felipesantiagoach-ops/cdp1802-8bit-computer/informe/Codigo fuente/contenido/reconocimientos.tex

% LOS RECONOCIMIENTOS
% -------------------

% Aquí se escribe la dedicatoria del proyecto y los agradecimientos. El entorno 'reconocimiento' tiene la estructura \begin{reconocimiento}{Dedicatoria} Agradecimientos \end{reconocimiento}

\begin{reconocimiento}{Dedicado a nuestras familias y amigos.}

\lipsum[5]

\begin{flushright}
\textit{Alegre Chamorro, Felipe Santiago}
\end{flushright}

\vspace{1cm}

Gracias a mis padres por haber hecho posible estudiar ingeniería, no habría sido posible sin ellos, y gracias a los amigos que hice y a las experiencias que tuvimos durante el transcurso de la carrera, que son, para mí, casi más importantes que la carrera en sí misma.

\begin{flushright}
\textit{Boher, Atilio}
\end{flushright}

\vspace{1cm}

\lipsum[5]

\begin{flushright}
\textit{Vera, Uriel Adrián}
\end{flushright}

\end{reconocimiento}
