felipesantiagoach-ops/cdp1802-8bit-computer/programas/sistema medio/Tx/notas.txt

no funcionaron en el sistema medio, si funicionaron algunos en el simulador, pero no se testearon todos
