felipesantiagoach-ops/cdp1802-8bit-computer/Poster_PyD_2022_Grupo_A.pdf

## ¿ COMO ERAN LAS PRIMERAS COMPUTADORAS ? COMPUTADORA BASADA EN EL PRIMER

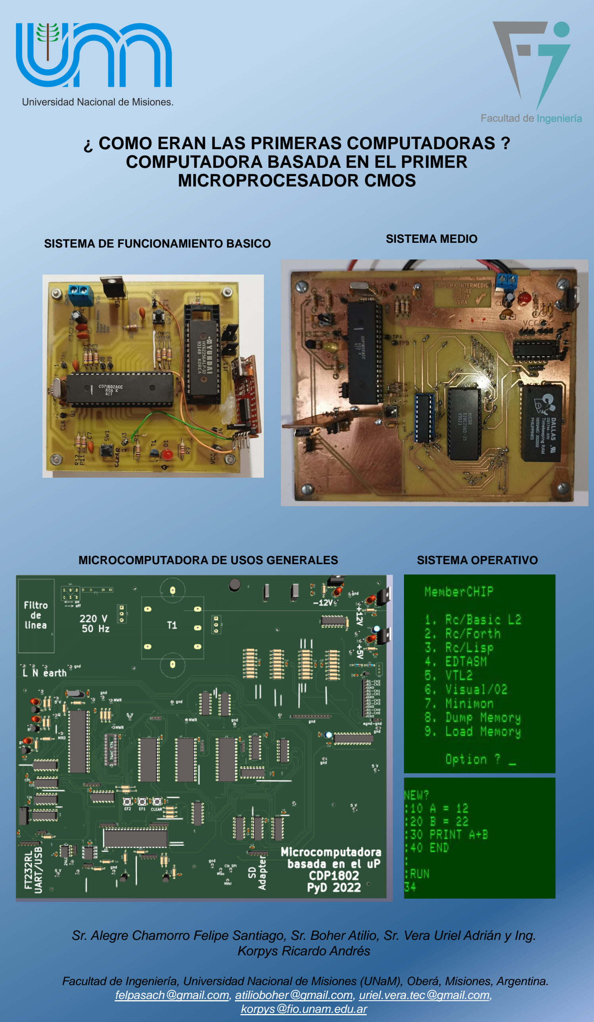
[picture p131: page 1]

## MICROPROCESADOR CMOS

SISTEMA DE FUNCIONAMIENTO BASICO

Sr. Alegre Chamorro Felipe Santiago, Sr. Boher Atilio, Sr. Vera Uriel Adrián y Ing. Korpys Ricardo Andrés

Facultad de Ingeniería, Universidad Nacional de Misiones (UNaM), Oberá, Misiones, Argentina. felpasach@gmail.com, atilioboher@gmail.com, uriel.vera.tec@gmail.com, korpys@fio.unam.edu.ar

SISTEMA MEDIO

MICROCOMPUTADORA DE USOS GENERALES | SISTEMA OPERATIVO
