felipesantiagoach-ops/cdp1802-8bit-computer/archivos_de_kicad/3_Sistema_final/PCB1.pdf

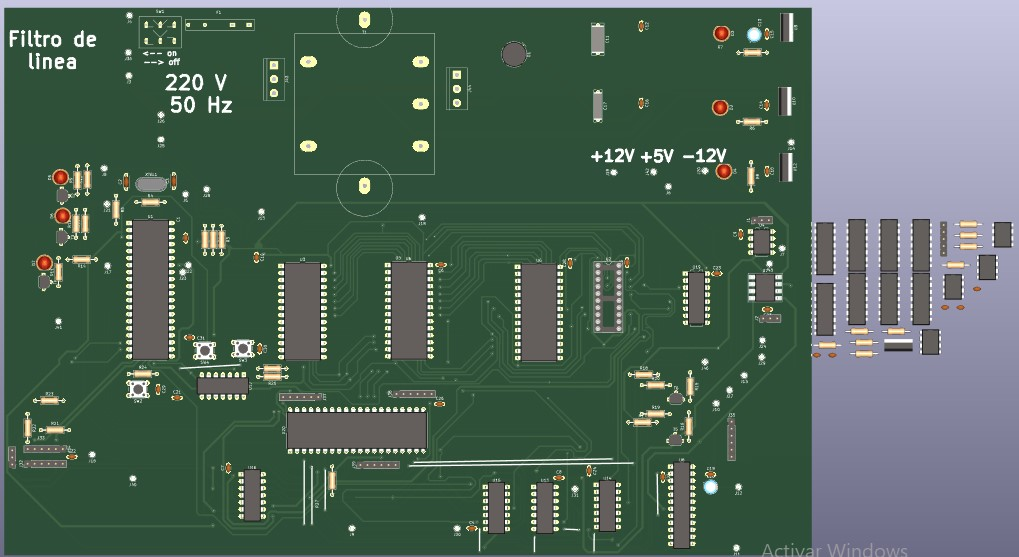
[picture p132: figure]
