felipesantiagoach-ops/cdp1802-8bit-computer/programas/sistema minimo/comunicacion serial/funcionamiento Tx serial.png

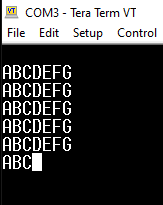
programas/sistema minimo/comunicacion serial/funcionamiento Tx serial.png
