felipesantiagoach-ops/cdp1802-8bit-computer/informe/Codigo fuente/imagenes/programa_1.pdf

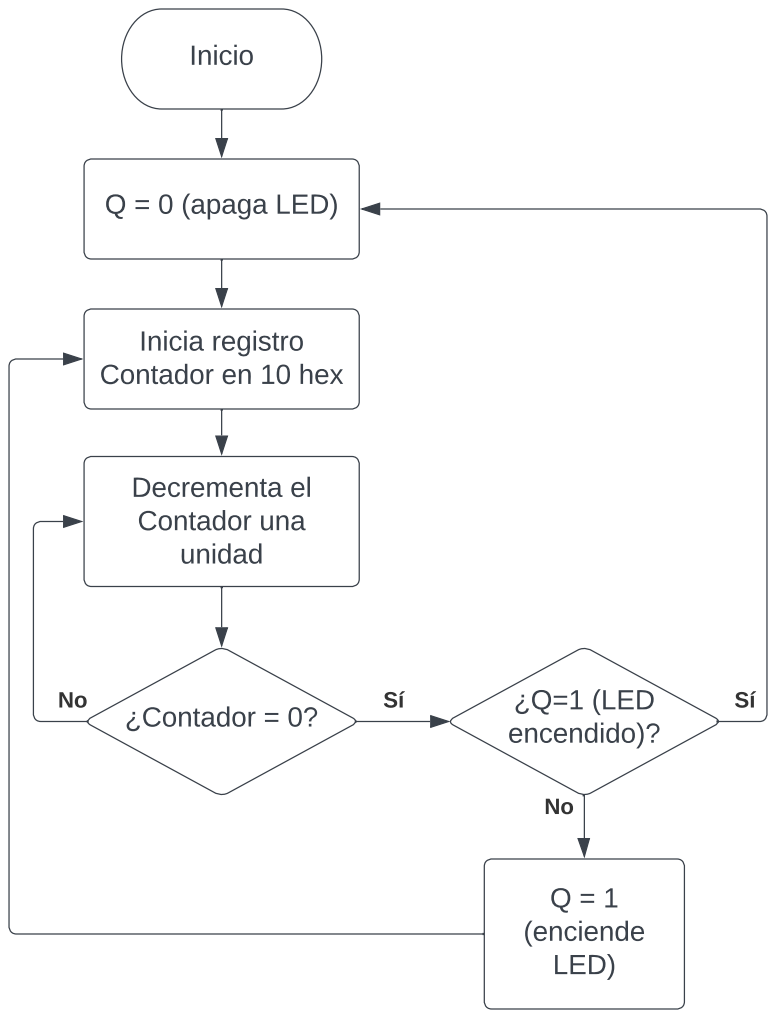
[picture p139: page 1]
Inicio; Q = 0 (apaga LED); Decrementa el Contador una unidad; ¿Contador = 0?; ¿Q=1 (LED; encendido)?; Q = 1 (enciende LED)

Inicia registro
Contador en 10 hex
