felipesantiagoach-ops/cdp1802-8bit-computer/informe/Codigo fuente/imagenes/programa_2.pdf

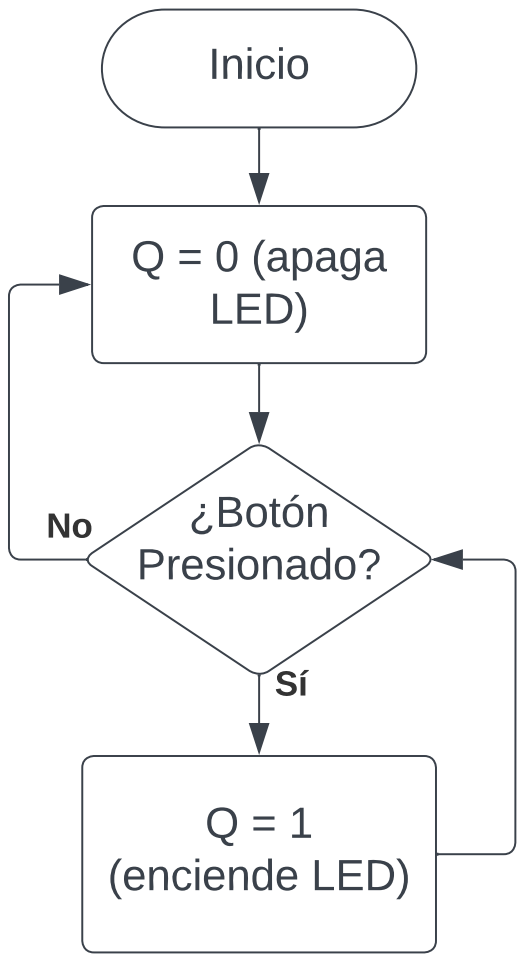
[picture p140: page 1]
Inicio; Q = 0 (apaga LED); ¿Botón Presionado?; Q = 1 (enciende LED)
