felipesantiagoach-ops/cdp1802-8bit-computer/informe/Codigo fuente/imagenes/programa_3.pdf

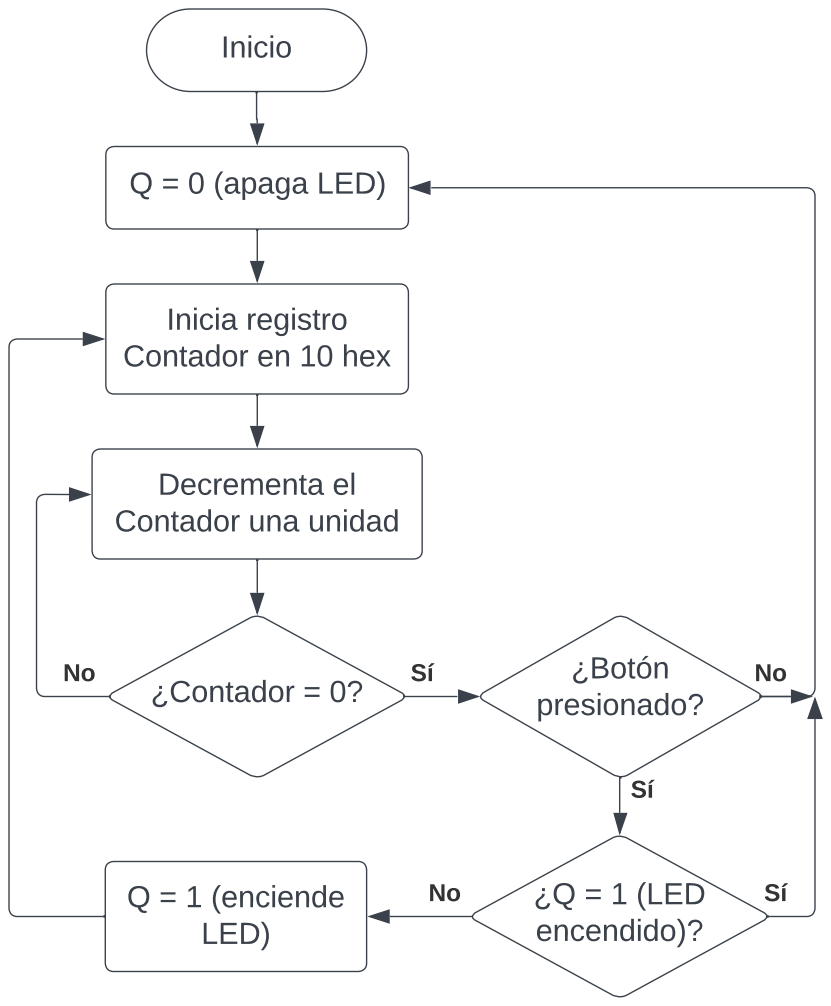
[picture p141: page 1]
Inicio; ¿Contador = 0?; Q = 0 (apaga LED); ¿Q = 1 (LED encendido)?; Q = 1 (enciende LED); ¿Botón presionado?

Inicia registro
Contador en 10 hex

Decrementa el
Contador una unidad
