felipesantiagoach-ops/cdp1802-8bit-computer/informe/Codigo fuente/imagenes/program_4_rut_de_trans.pdf

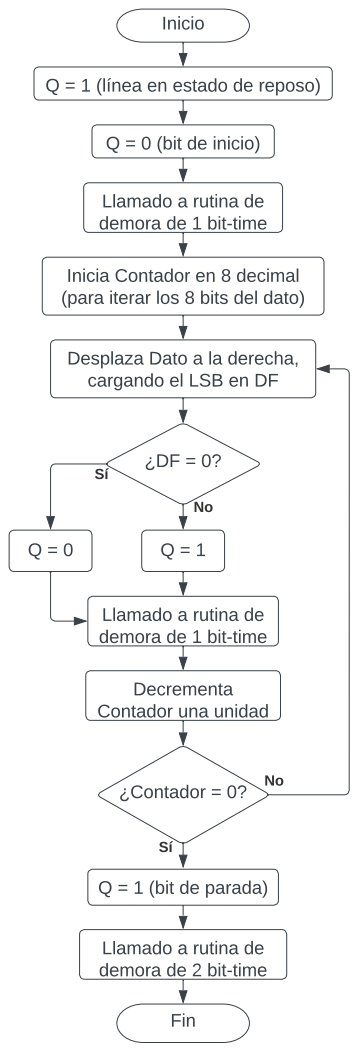
[picture p145: page 1]
Inicio; ¿Contador = 0?; Fin

Q = 1 (línea en estado de reposo)

Q = 0 (bit de inicio)

Llamado a rutina de
demora de 1 bit-time

Inicia Contador en 8 decimal
(para iterar los 8 bits del dato)

Desplaza Dato a la derecha,
cargando el LSB en DF

Decrementa
Contador una unidad

Q = 1 (bit de parada)

demora de 2 bit-time
