felipesantiagoach-ops/cdp1802-8bit-computer/informe/Codigo fuente/imagenes/programa_4_main.pdf

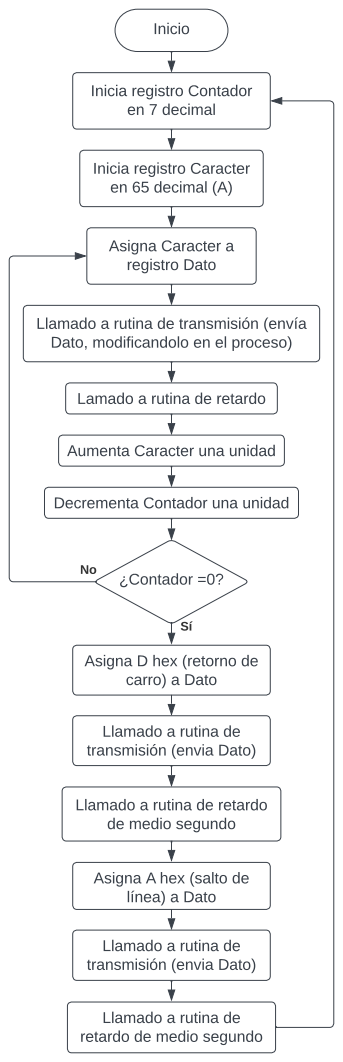
[picture p146: page 1]
Inicio; Asigna Caracter a registro Dato; ¿Contador =0?

Inicia registro Contador
en 7 decimal

Inicia registro Caracter
en 65 decimal (A)

Llamado a rutina de transmisión (envía
Dato, modificandolo en el proceso)

Lamado a rutina de retardo

Aumenta Caracter una unidad

Decrementa Contador una unidad

Asigna D hex (retorno de
carro) a Dato

Llamado a rutina de
transmisión (envia Dato)

Llamado a rutina de retardo
de medio segundo

Asigna A hex (salto de
línea) a Dato

retardo de medio segundo
