felipesantiagoach-ops/cdp1802-8bit-computer/informe/Codigo fuente/imagenes/EsquematicosSF/Esquematico (1).pdf

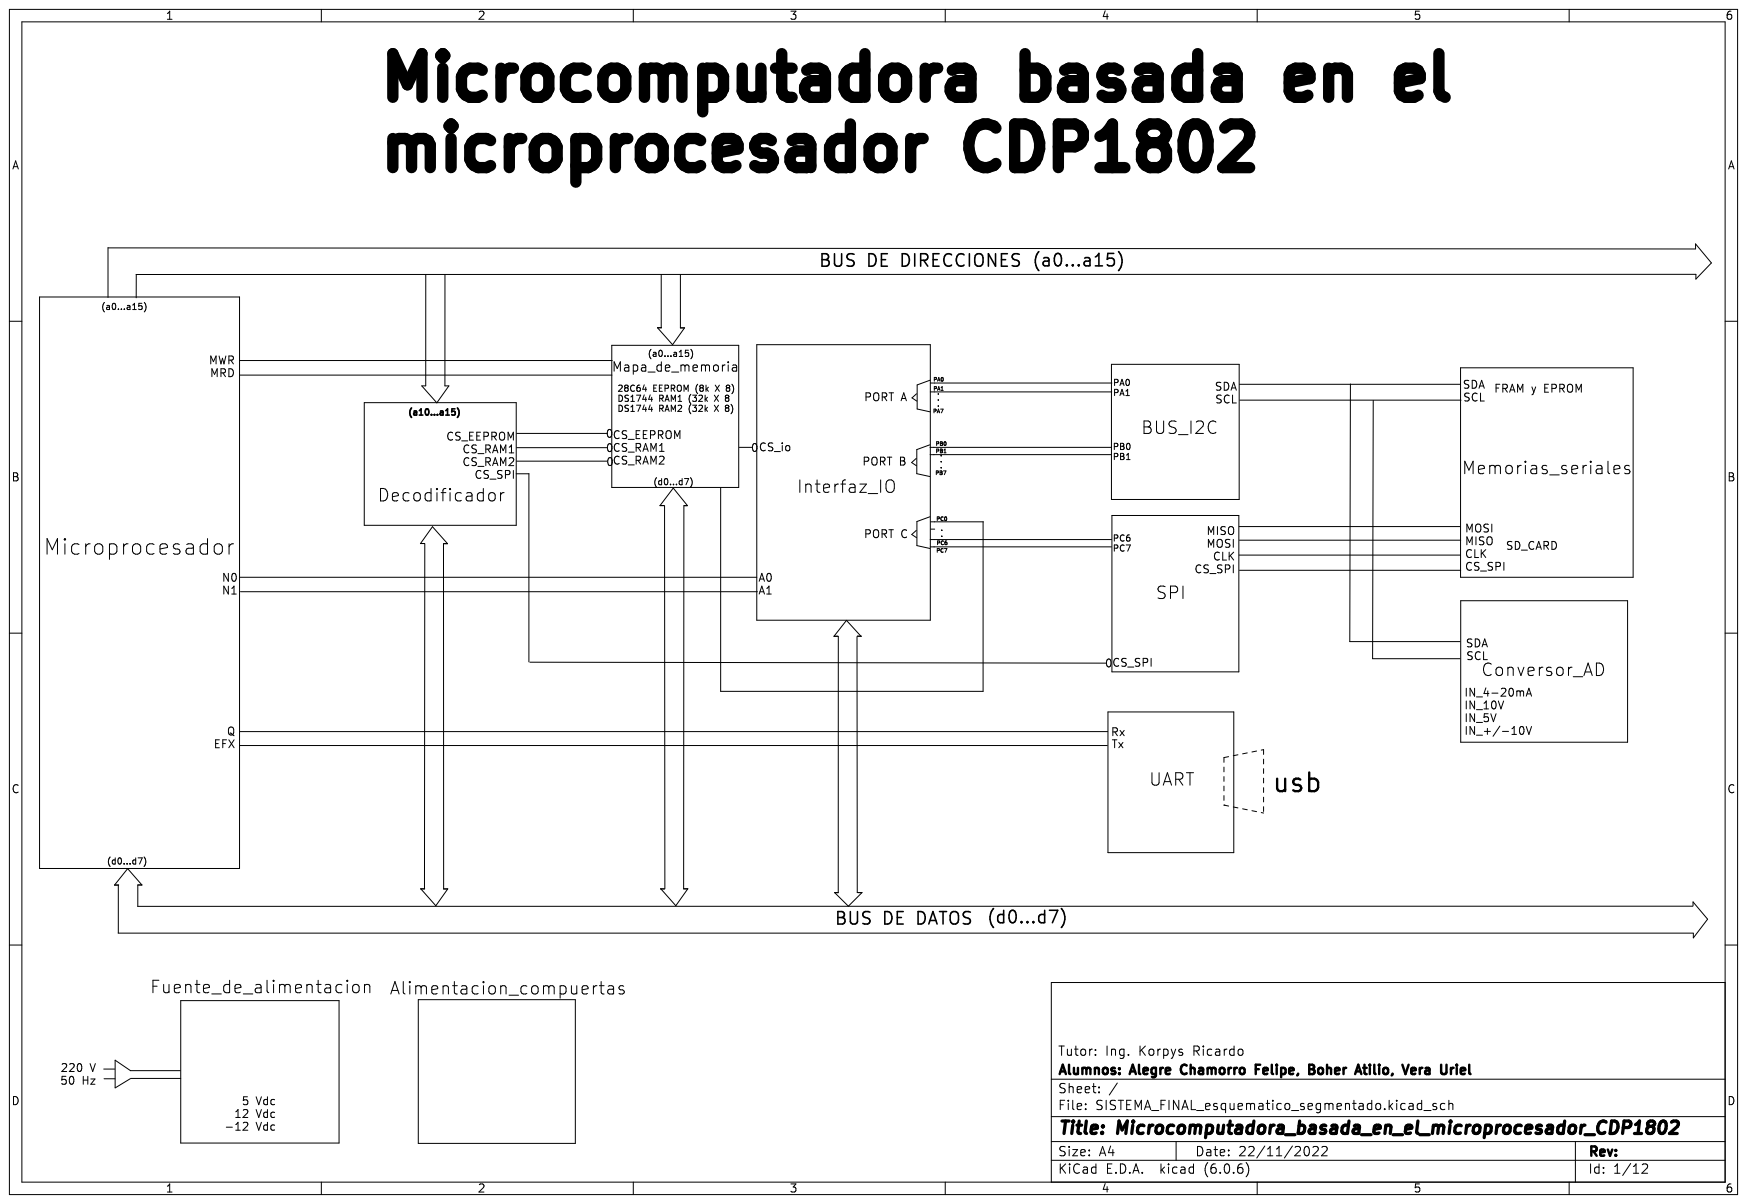
[picture p147: page 1]
