felipesantiagoach-ops/cdp1802-8bit-computer/informe/Codigo fuente/imagenes/EsquematicosSF/Esquematico (10).pdf

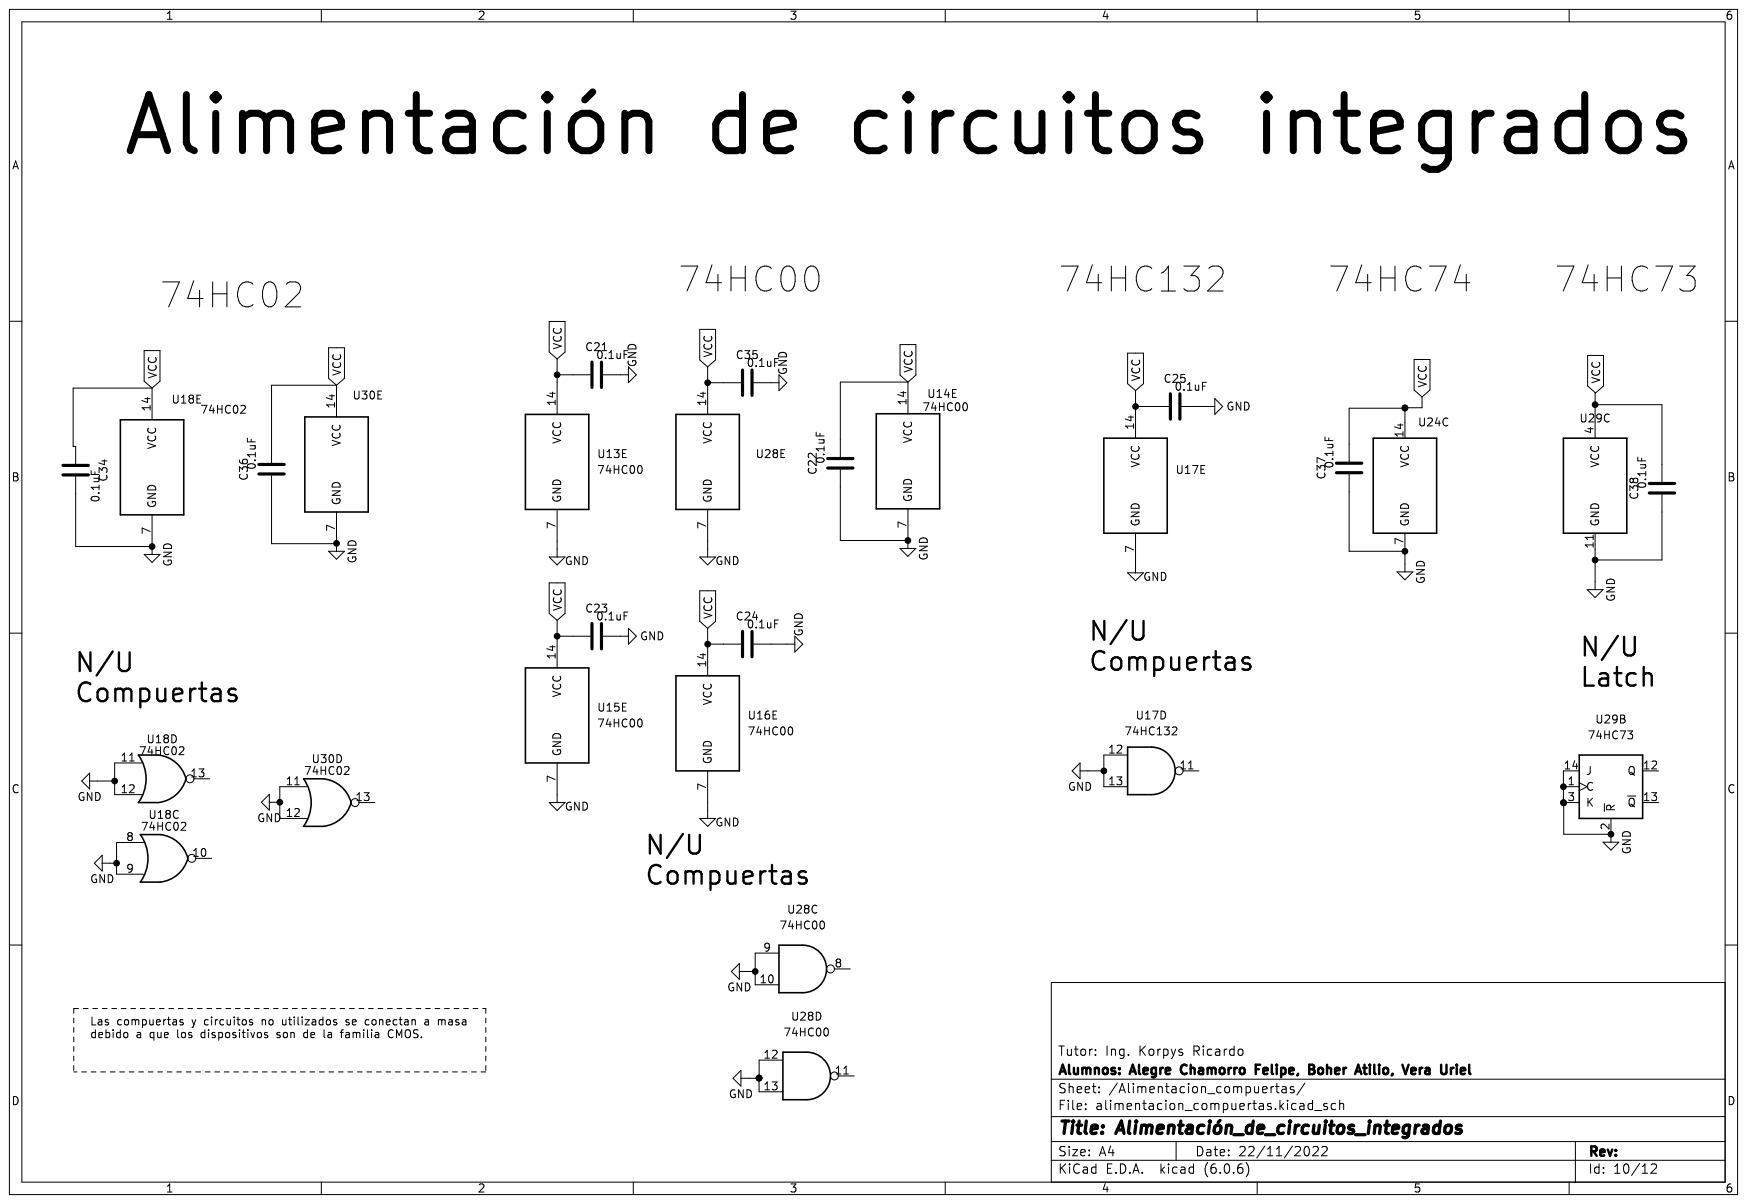
[picture p148: page 1]
