felipesantiagoach-ops/cdp1802-8bit-computer/informe/Codigo fuente/imagenes/EsquematicosSF/Esquematico (11).pdf

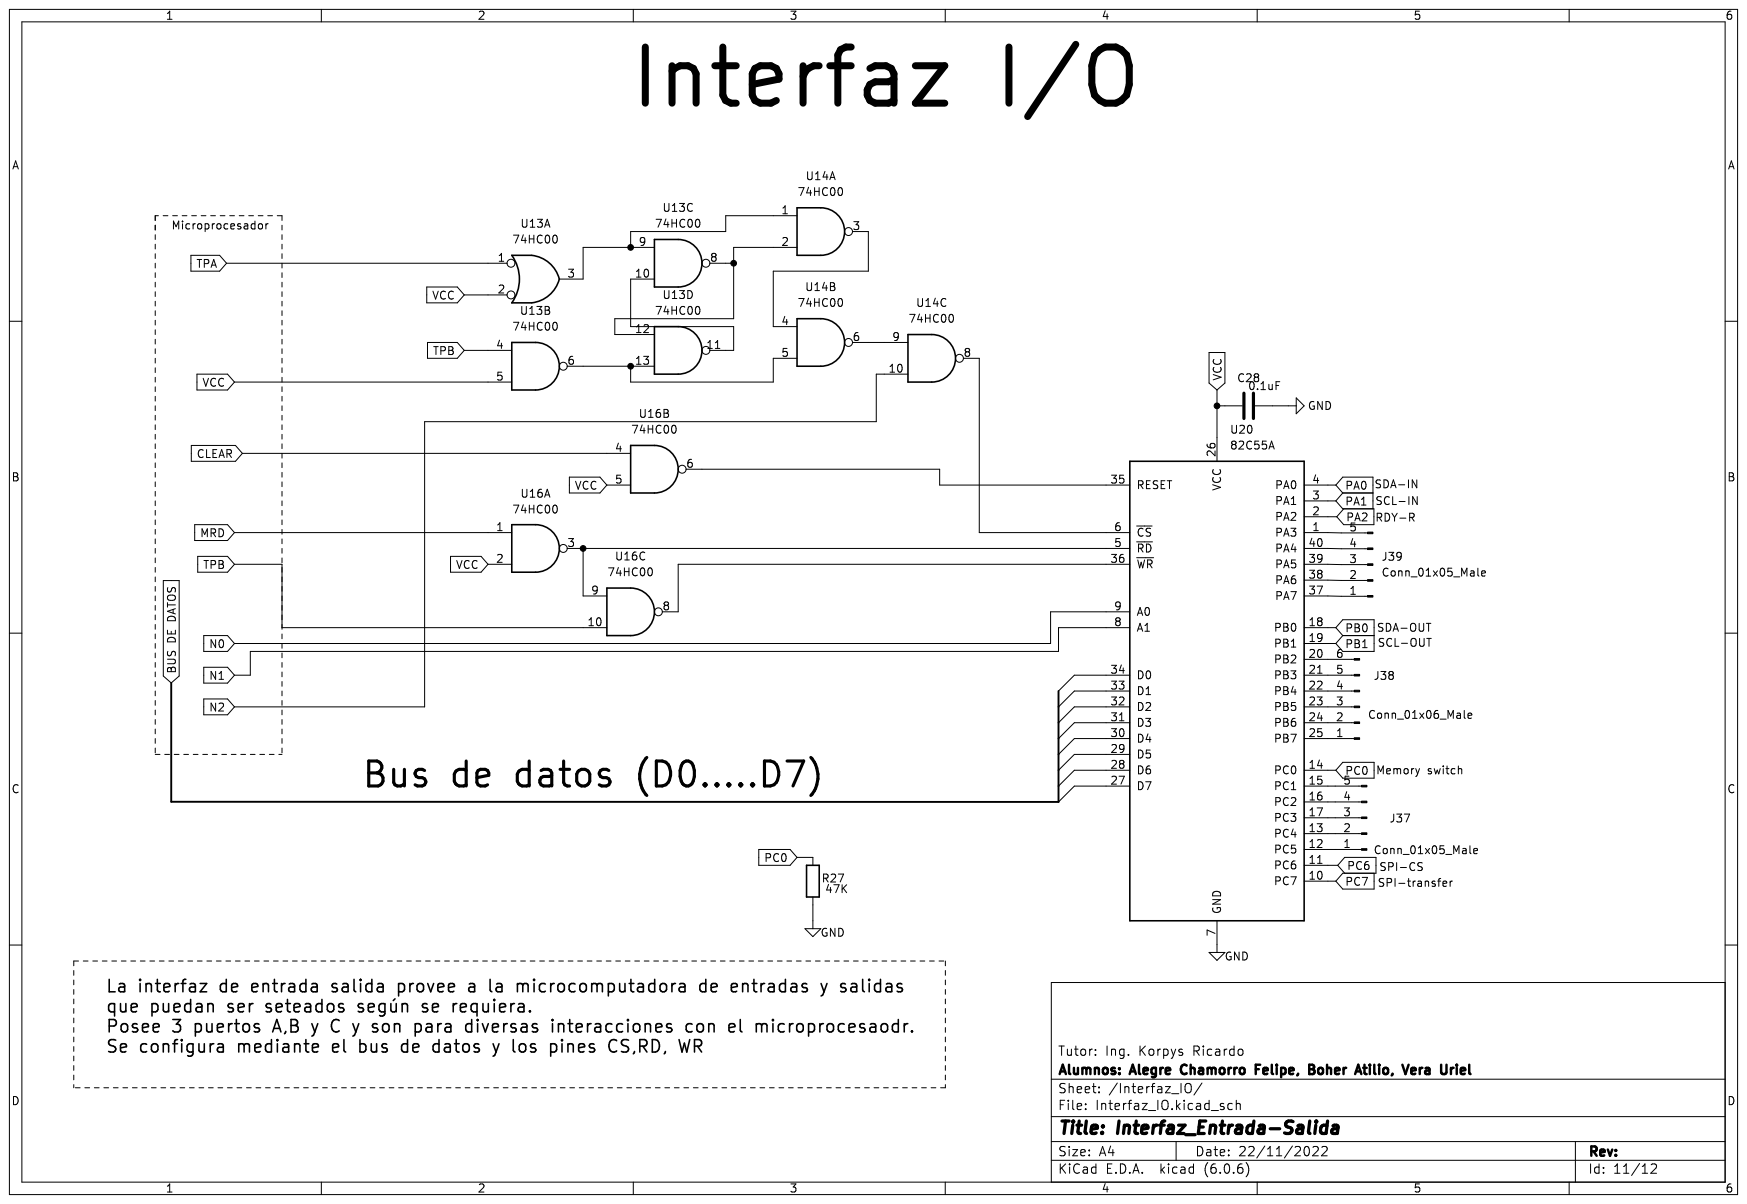
[picture p149: page 1]
