felipesantiagoach-ops/cdp1802-8bit-computer/informe/Codigo fuente/imagenes/EsquematicosSF/Esquematico (12).pdf

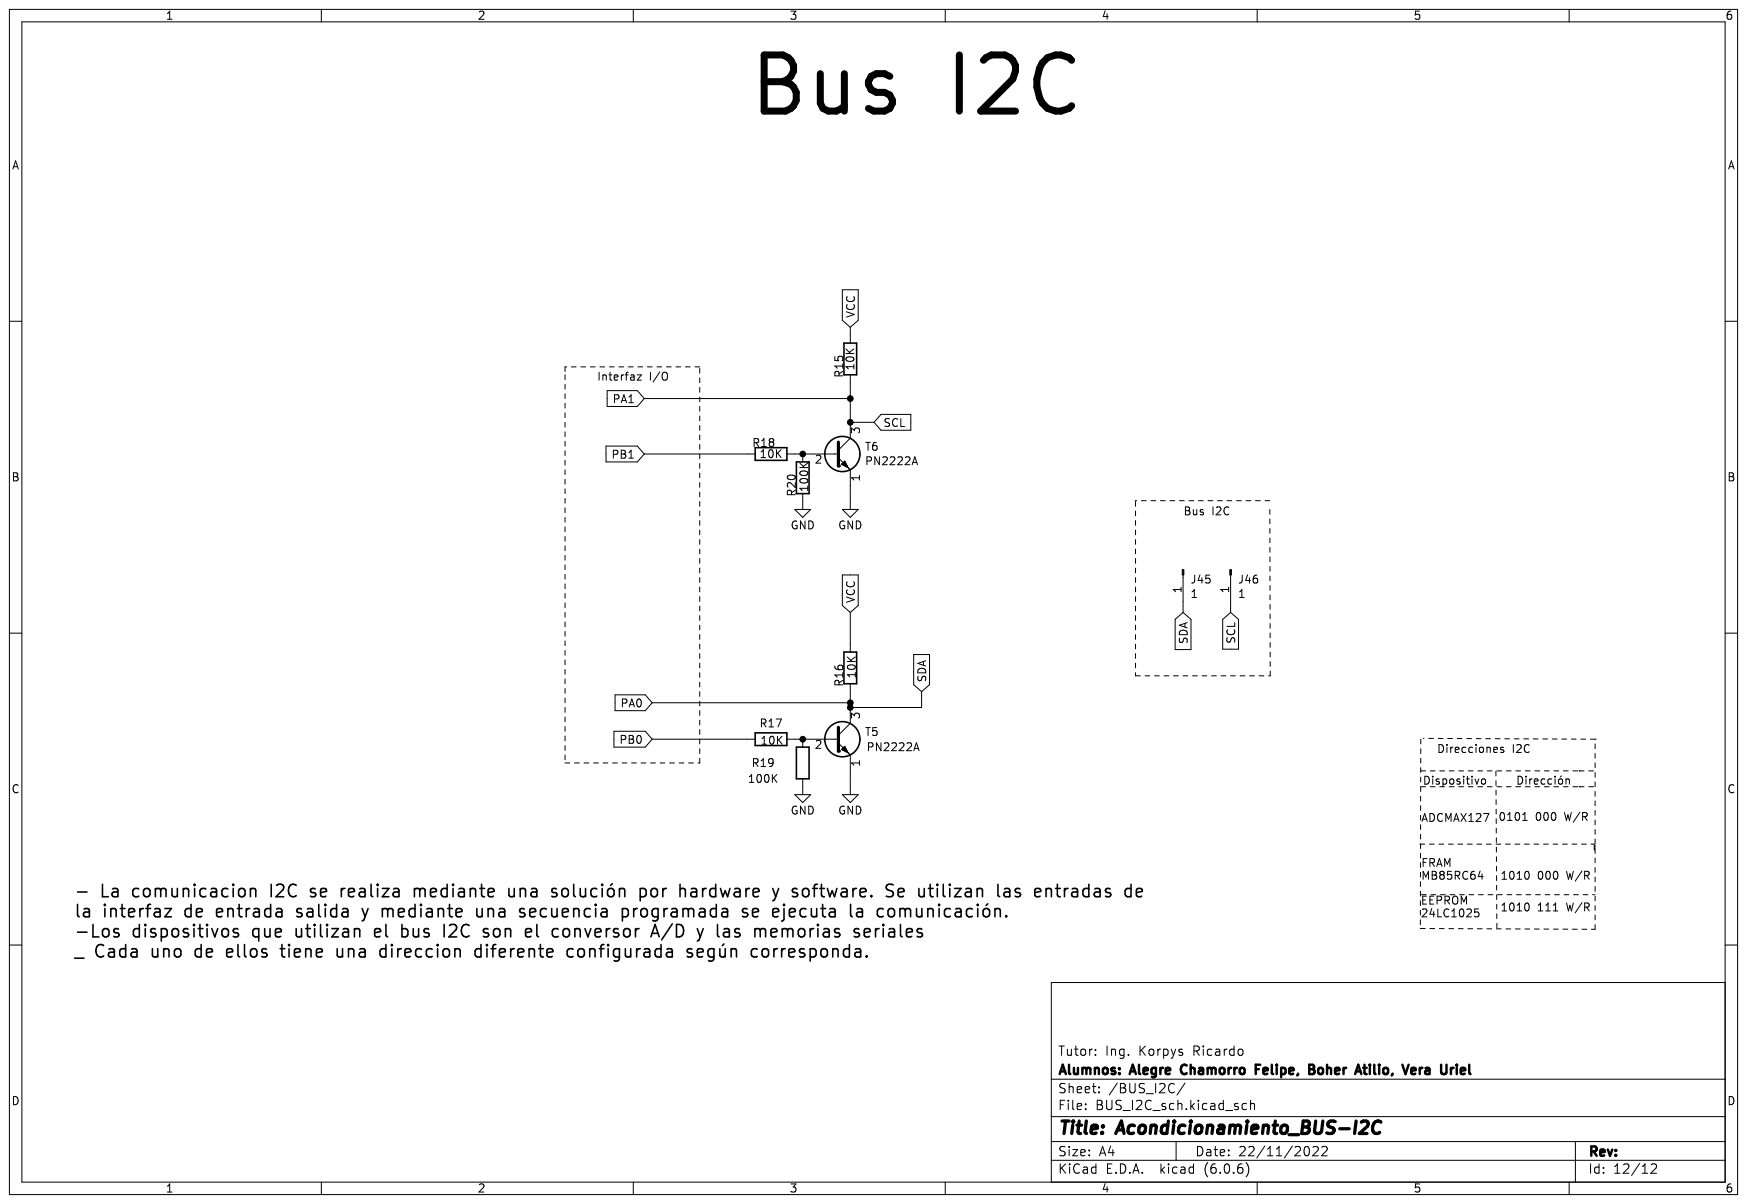
[picture p150: page 1]
