felipesantiagoach-ops/cdp1802-8bit-computer/informe/Codigo fuente/imagenes/EsquematicosSF/Esquematico (2).pdf

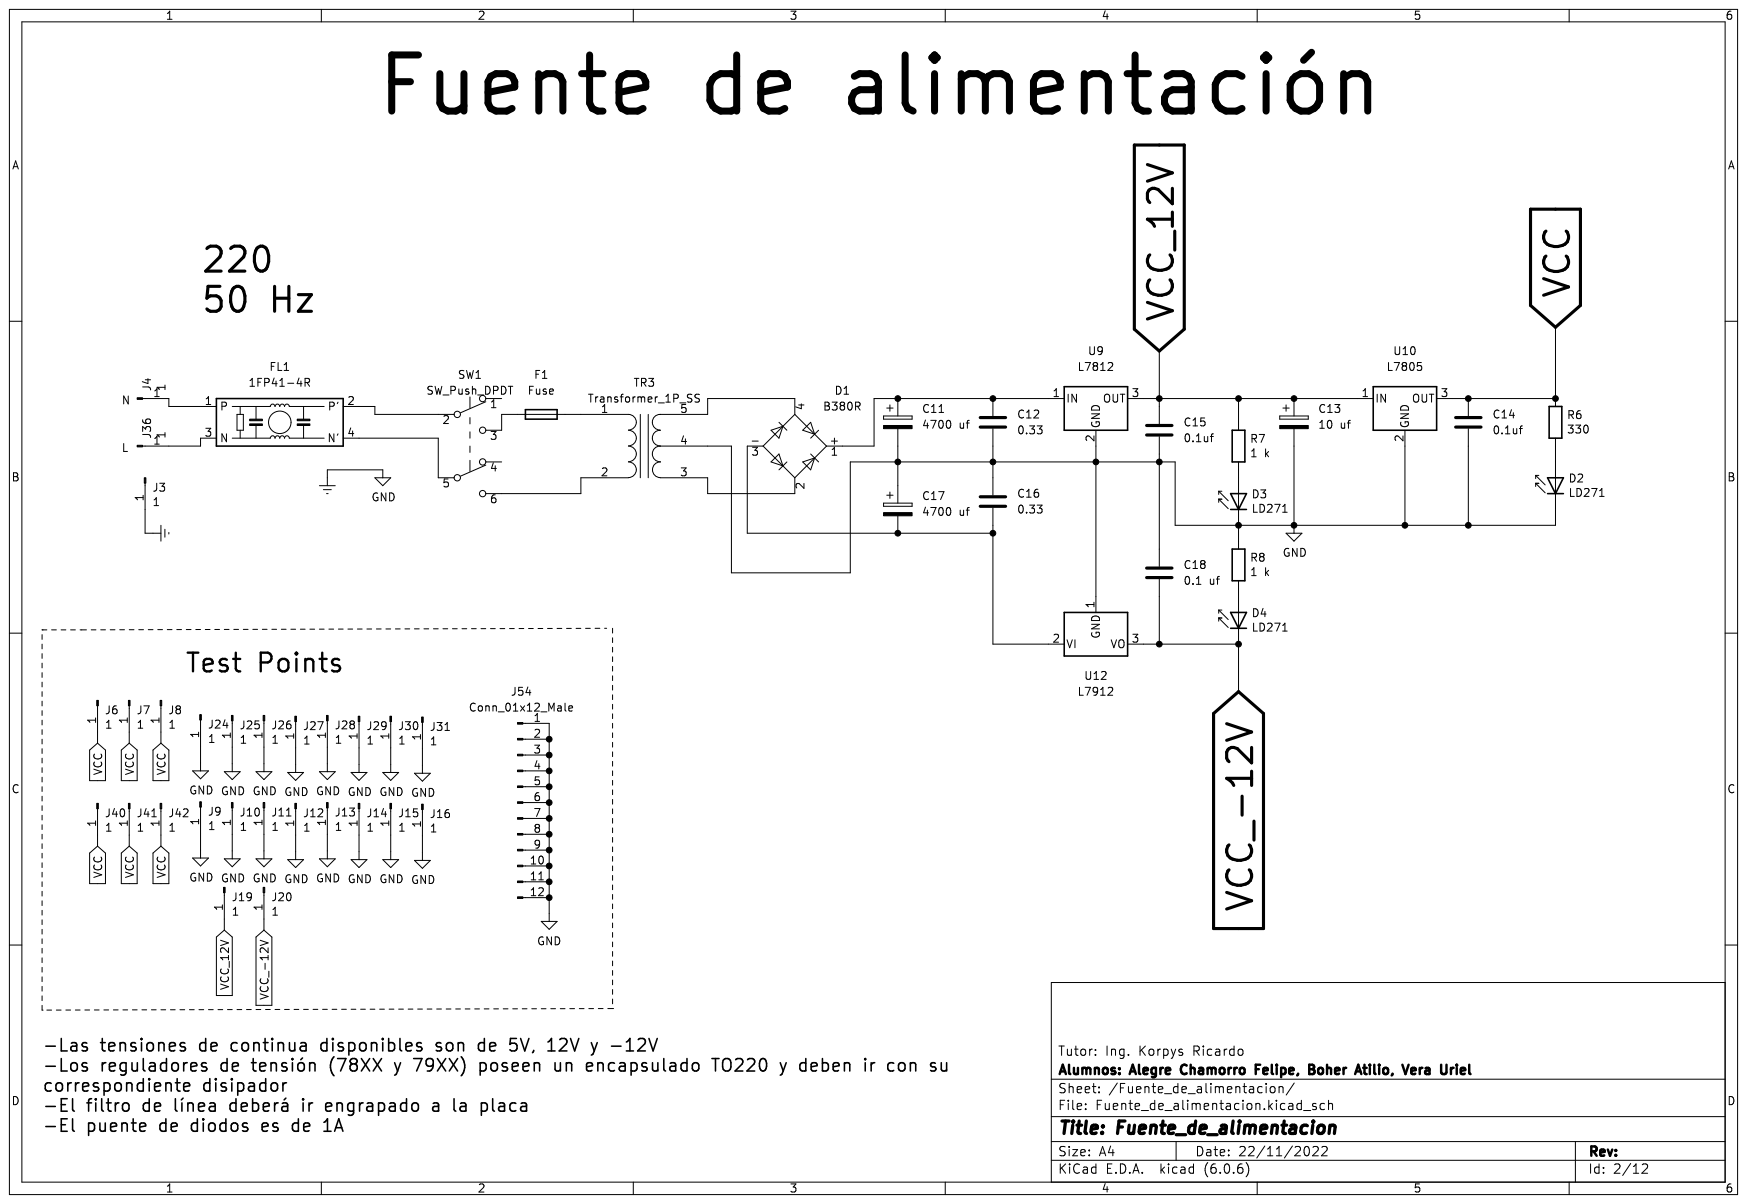
[picture p151: page 1]
