felipesantiagoach-ops/cdp1802-8bit-computer/informe/Codigo fuente/imagenes/EsquematicosSF/PCB_atras.pdf

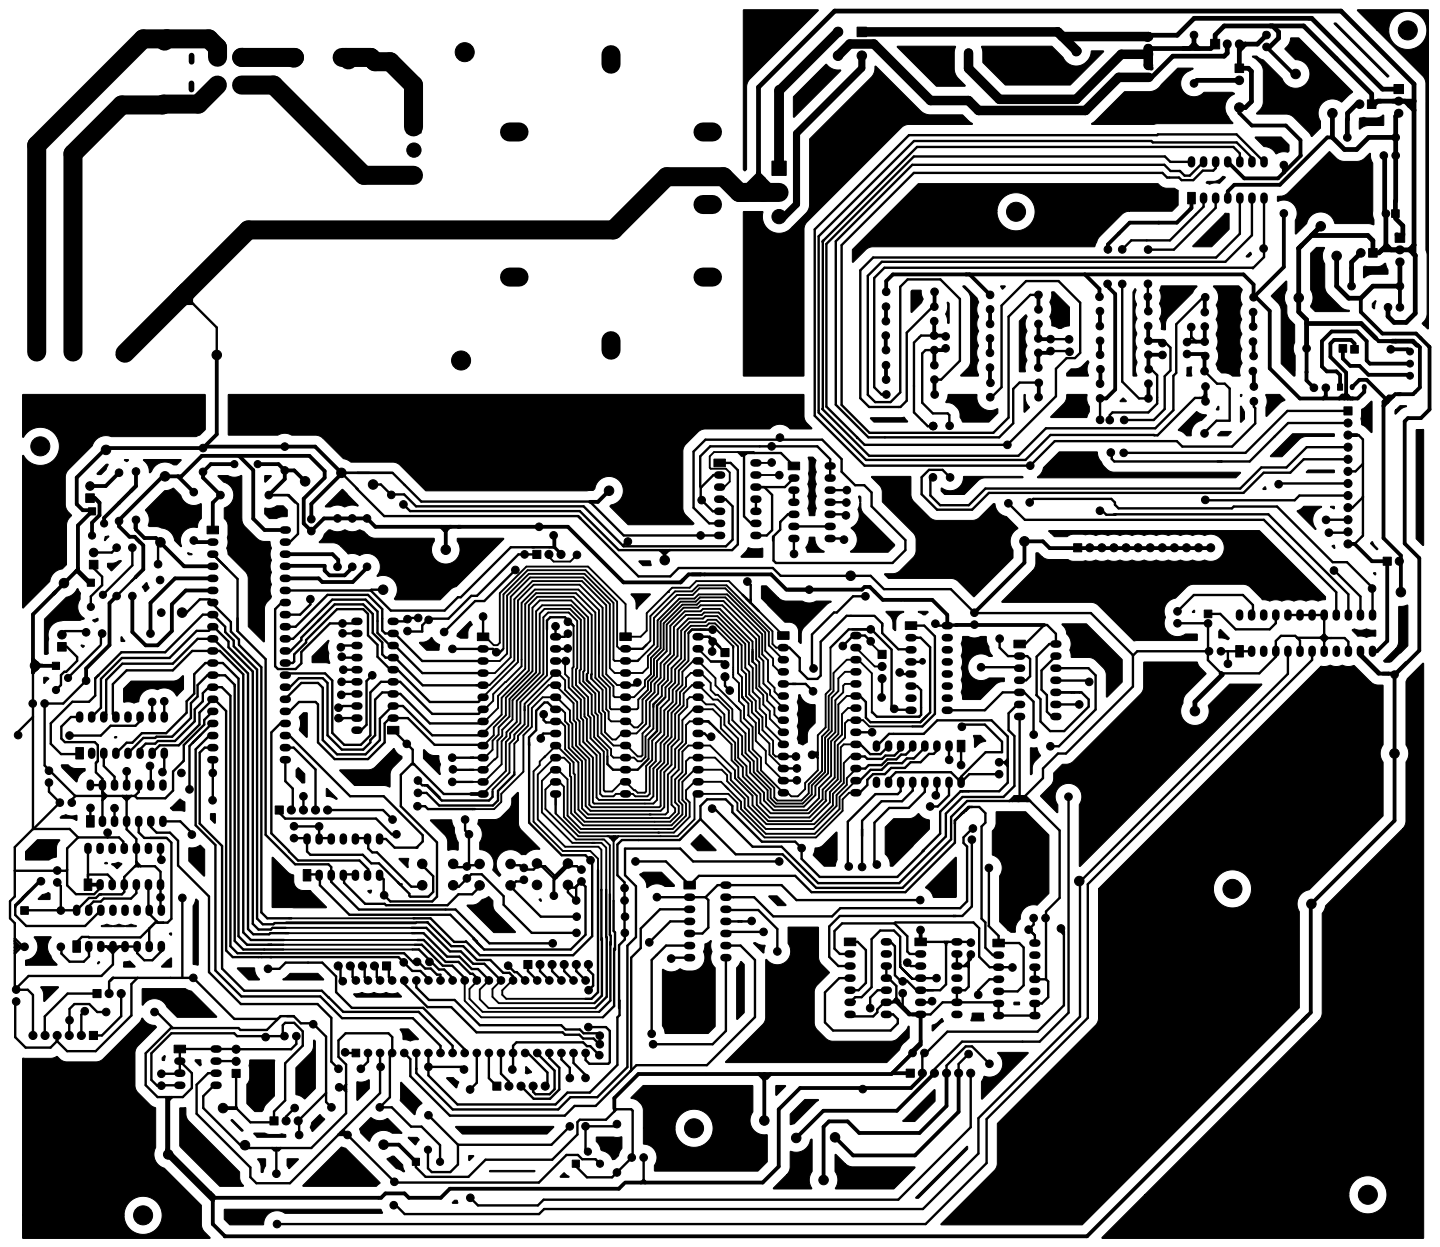
[picture p159: page 1]
