felipesantiagoach-ops/cdp1802-8bit-computer/informe/Codigo fuente/imagenes/EsquematicosSF/PCB_frente.pdf

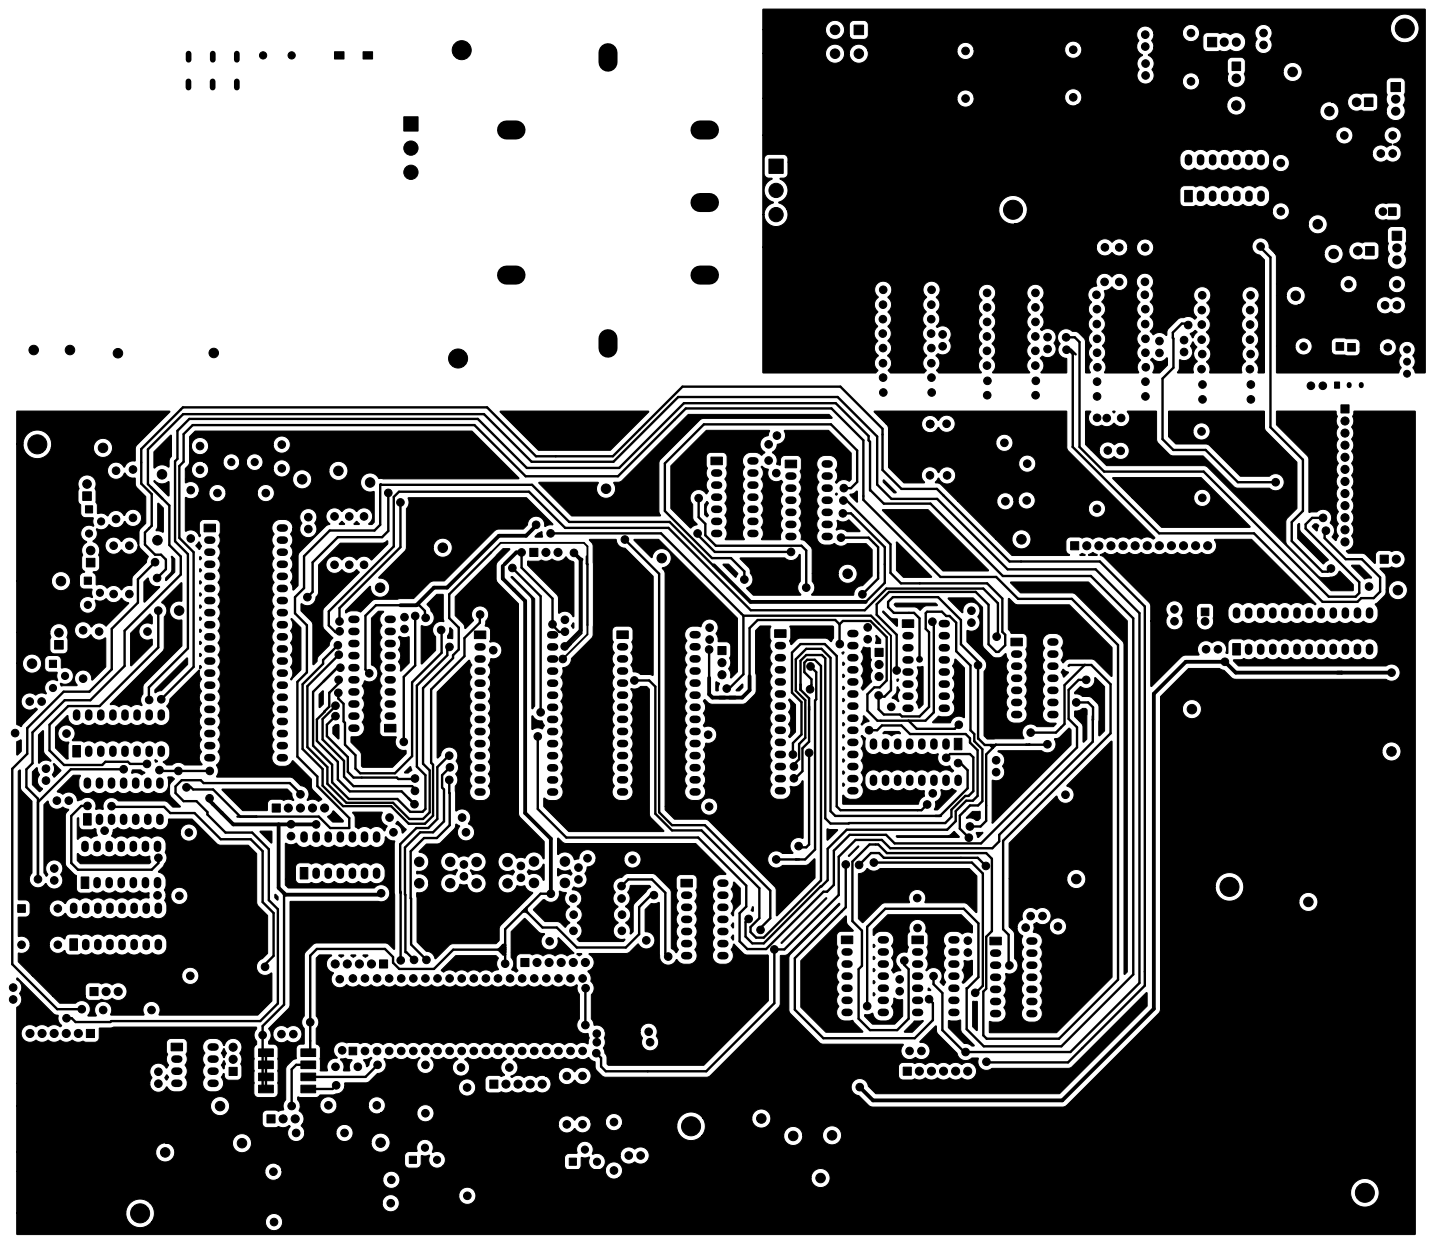
[picture p160: page 1]
