felipesantiagoach-ops/cdp1802-8bit-computer/informe/Codigo fuente/imagenes/EsquematicosSF/PCB_mascara.pdf

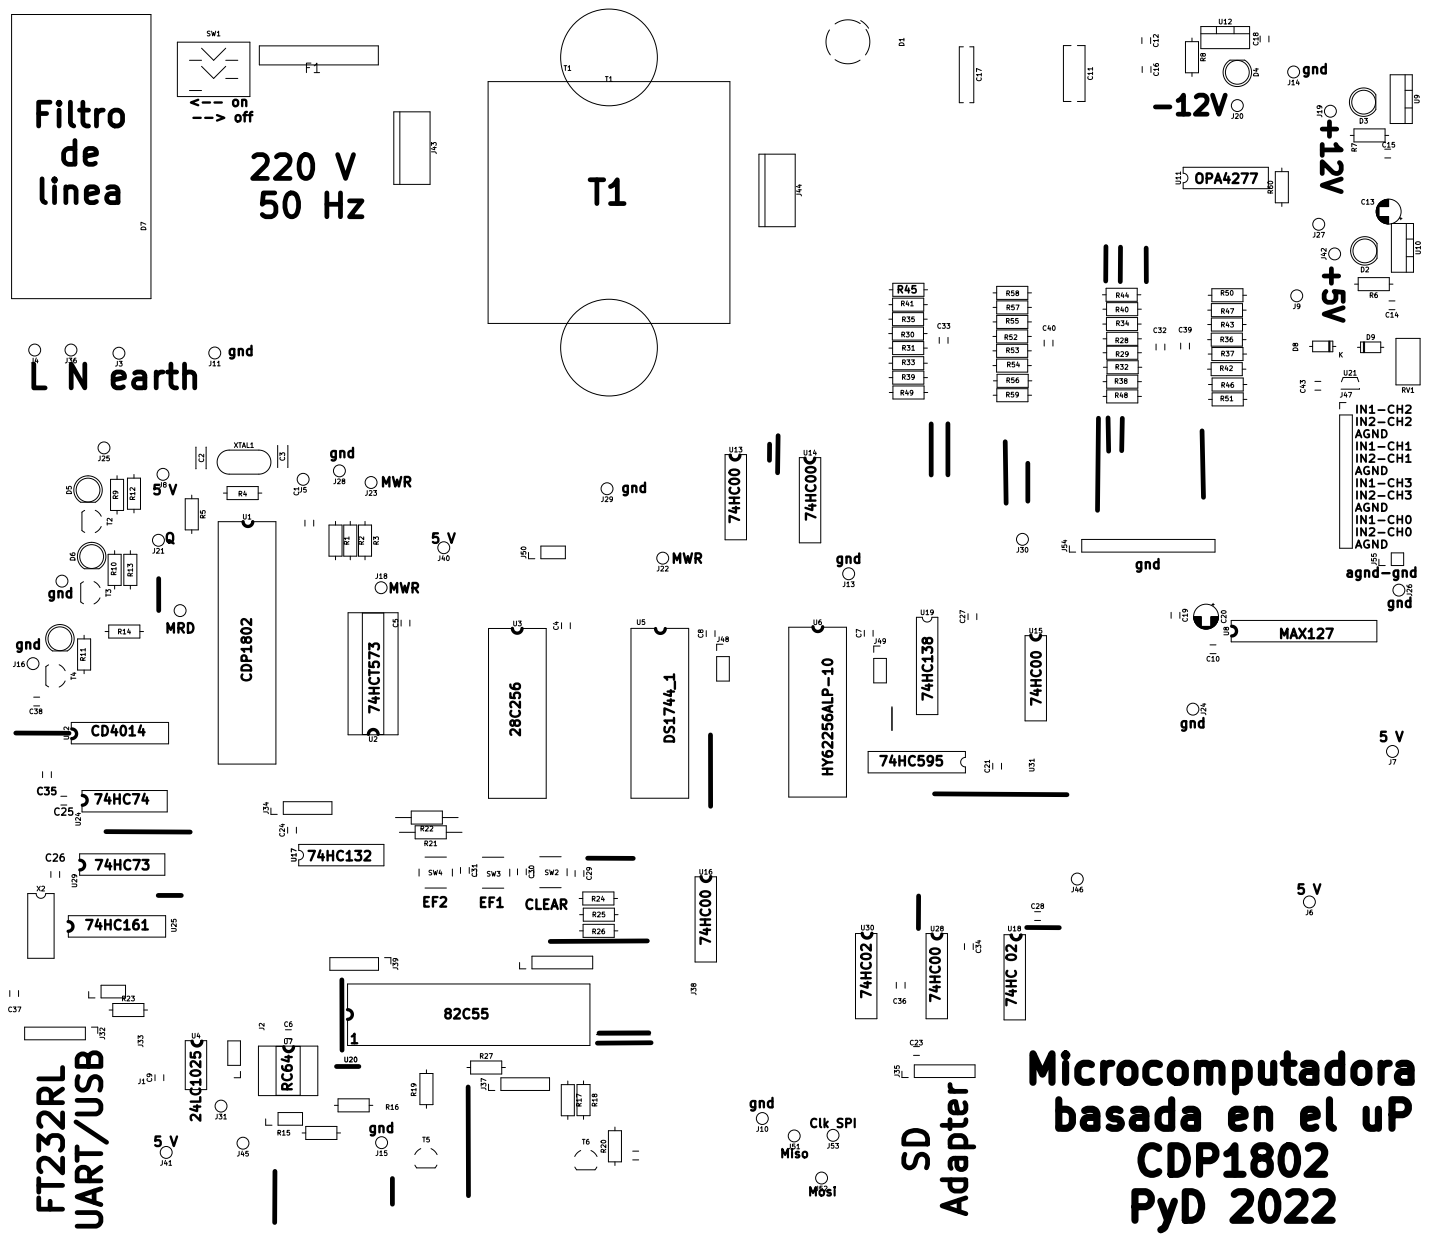
[picture p161: page 1]
