felipesantiagoach-ops/cdp1802-8bit-computer/informe/Codigo fuente/imagenes/imagenes_caratula/derecha-eps-converted-to.pdf

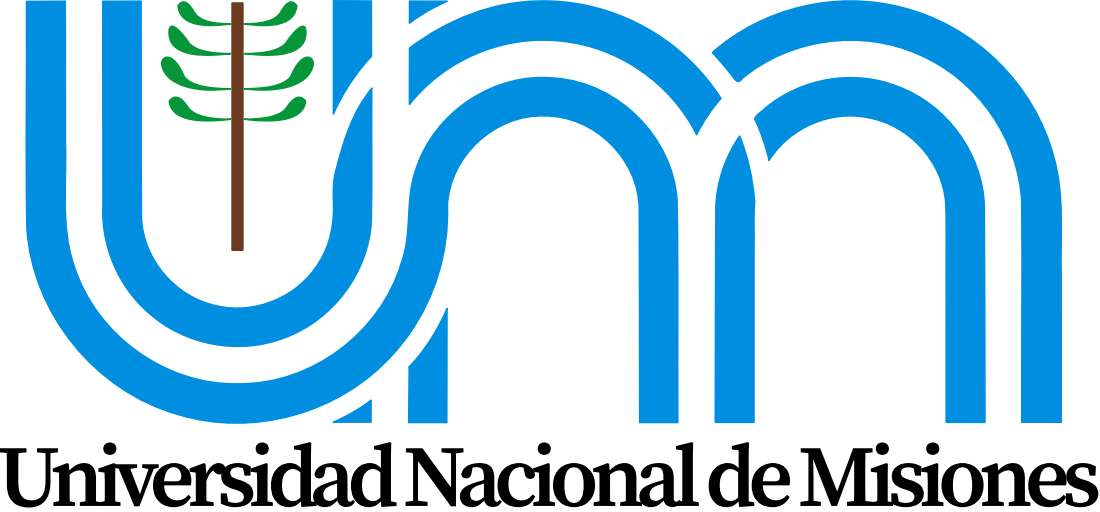
[picture p162: page 1]
