felipesantiagoach-ops/cdp1802-8bit-computer/informe/Codigo fuente/imagenes/imagenes_caratula/izquierda-eps-converted-to.pdf

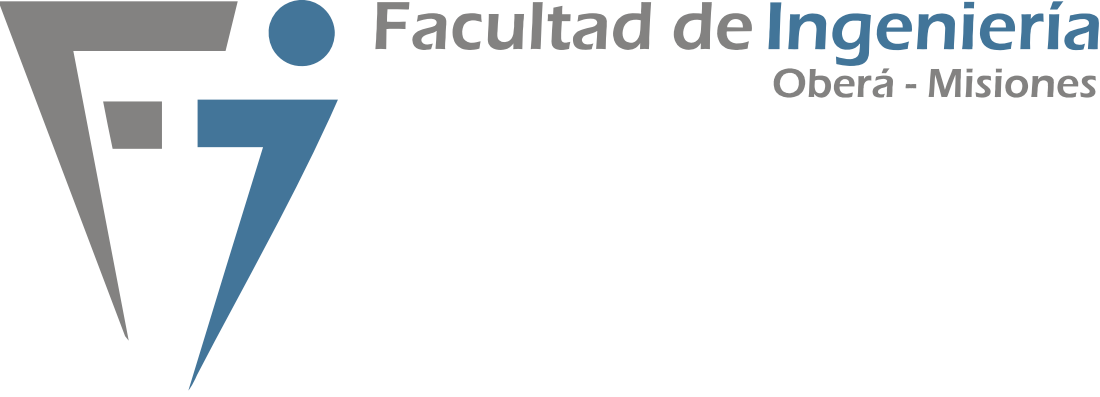
[picture p163: page 1]
