felipesantiagoach-ops/cdp1802-8bit-computer/archivos_de_kicad/1_Sistema_minimo/ParteArribaPCB.pdf

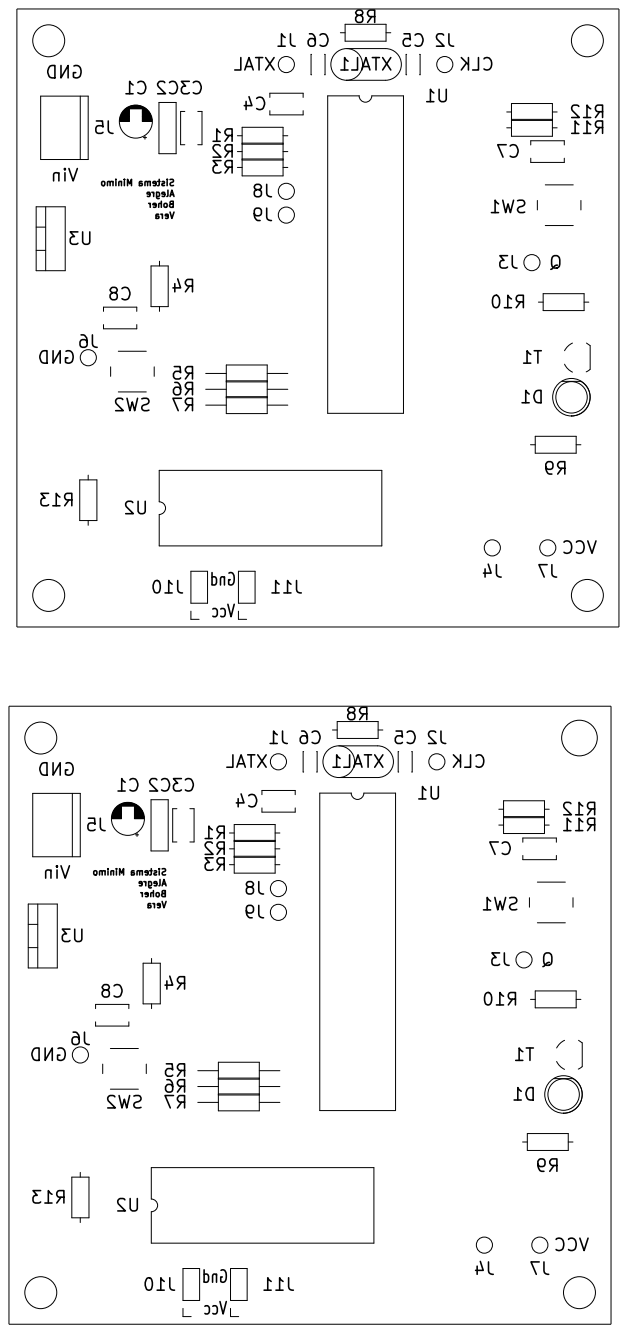
[picture p164: page 1]
