felipesantiagoach-ops/cdp1802-8bit-computer/archivos_de_kicad/2_Sistema_medio/Bottom_placa.pdf

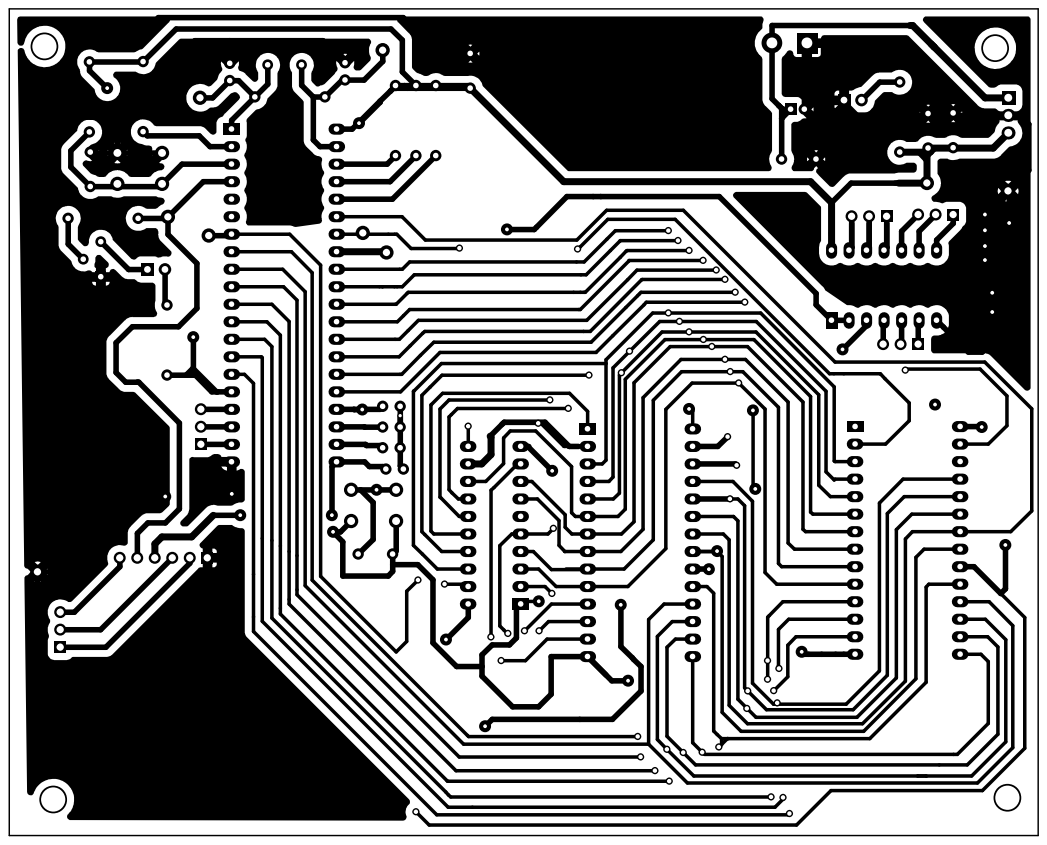
[picture p165: page 1]
