felipesantiagoach-ops/cdp1802-8bit-computer/archivos_de_kicad/2_Sistema_medio/Front_placa.pdf

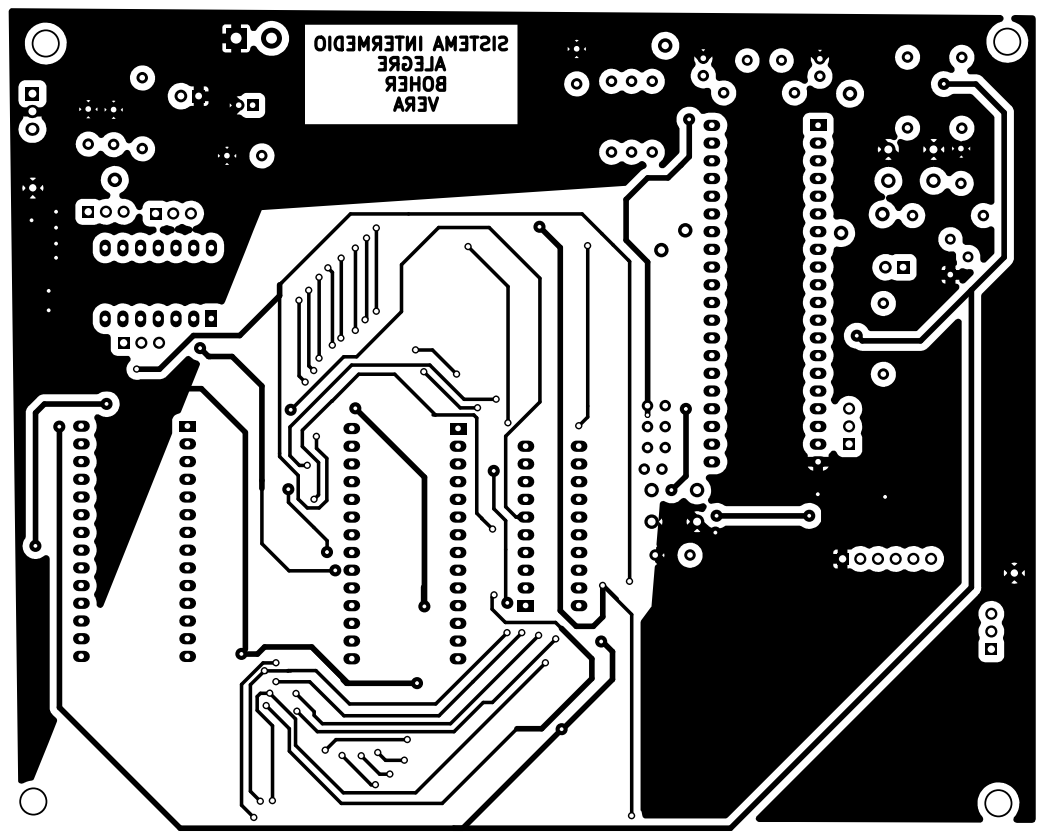
[picture p166: page 1]
