felipesantiagoach-ops/cdp1802-8bit-computer/archivos_de_kicad/2_Sistema_medio/mascara.pdf

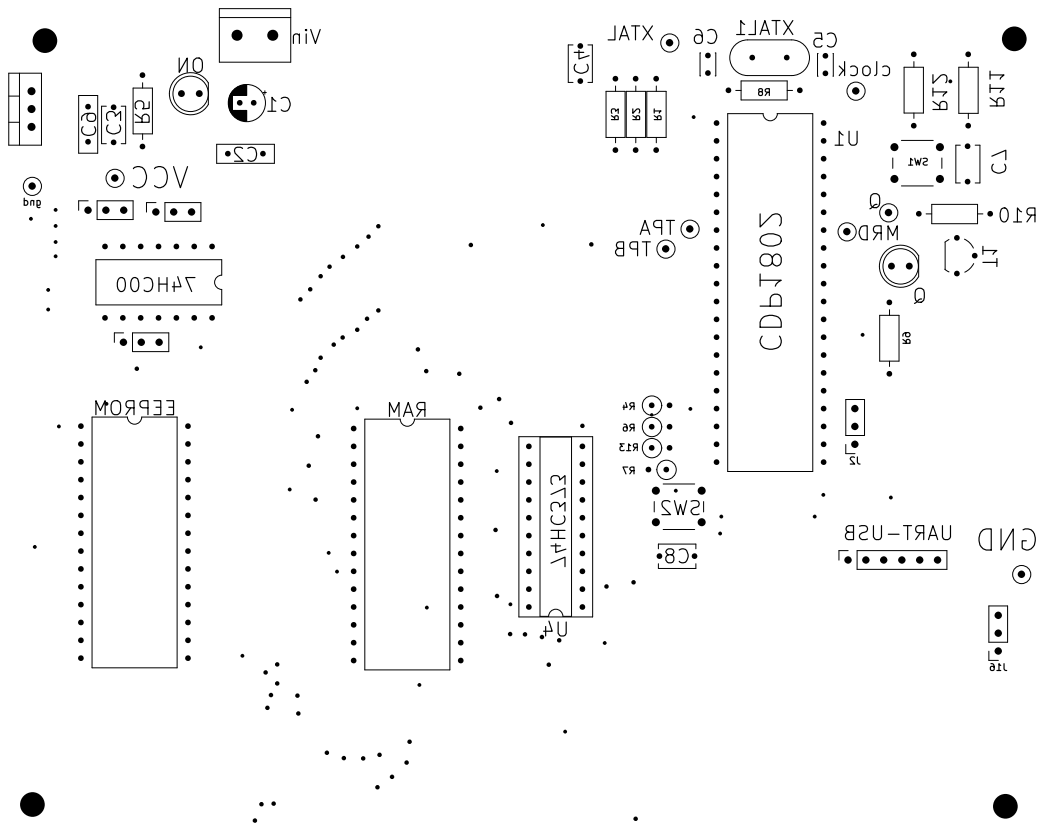
[picture p167: page 1]
