felipesantiagoach-ops/cdp1802-8bit-computer/archivos_de_kicad/2_Sistema_medio/Presentcion.pdf

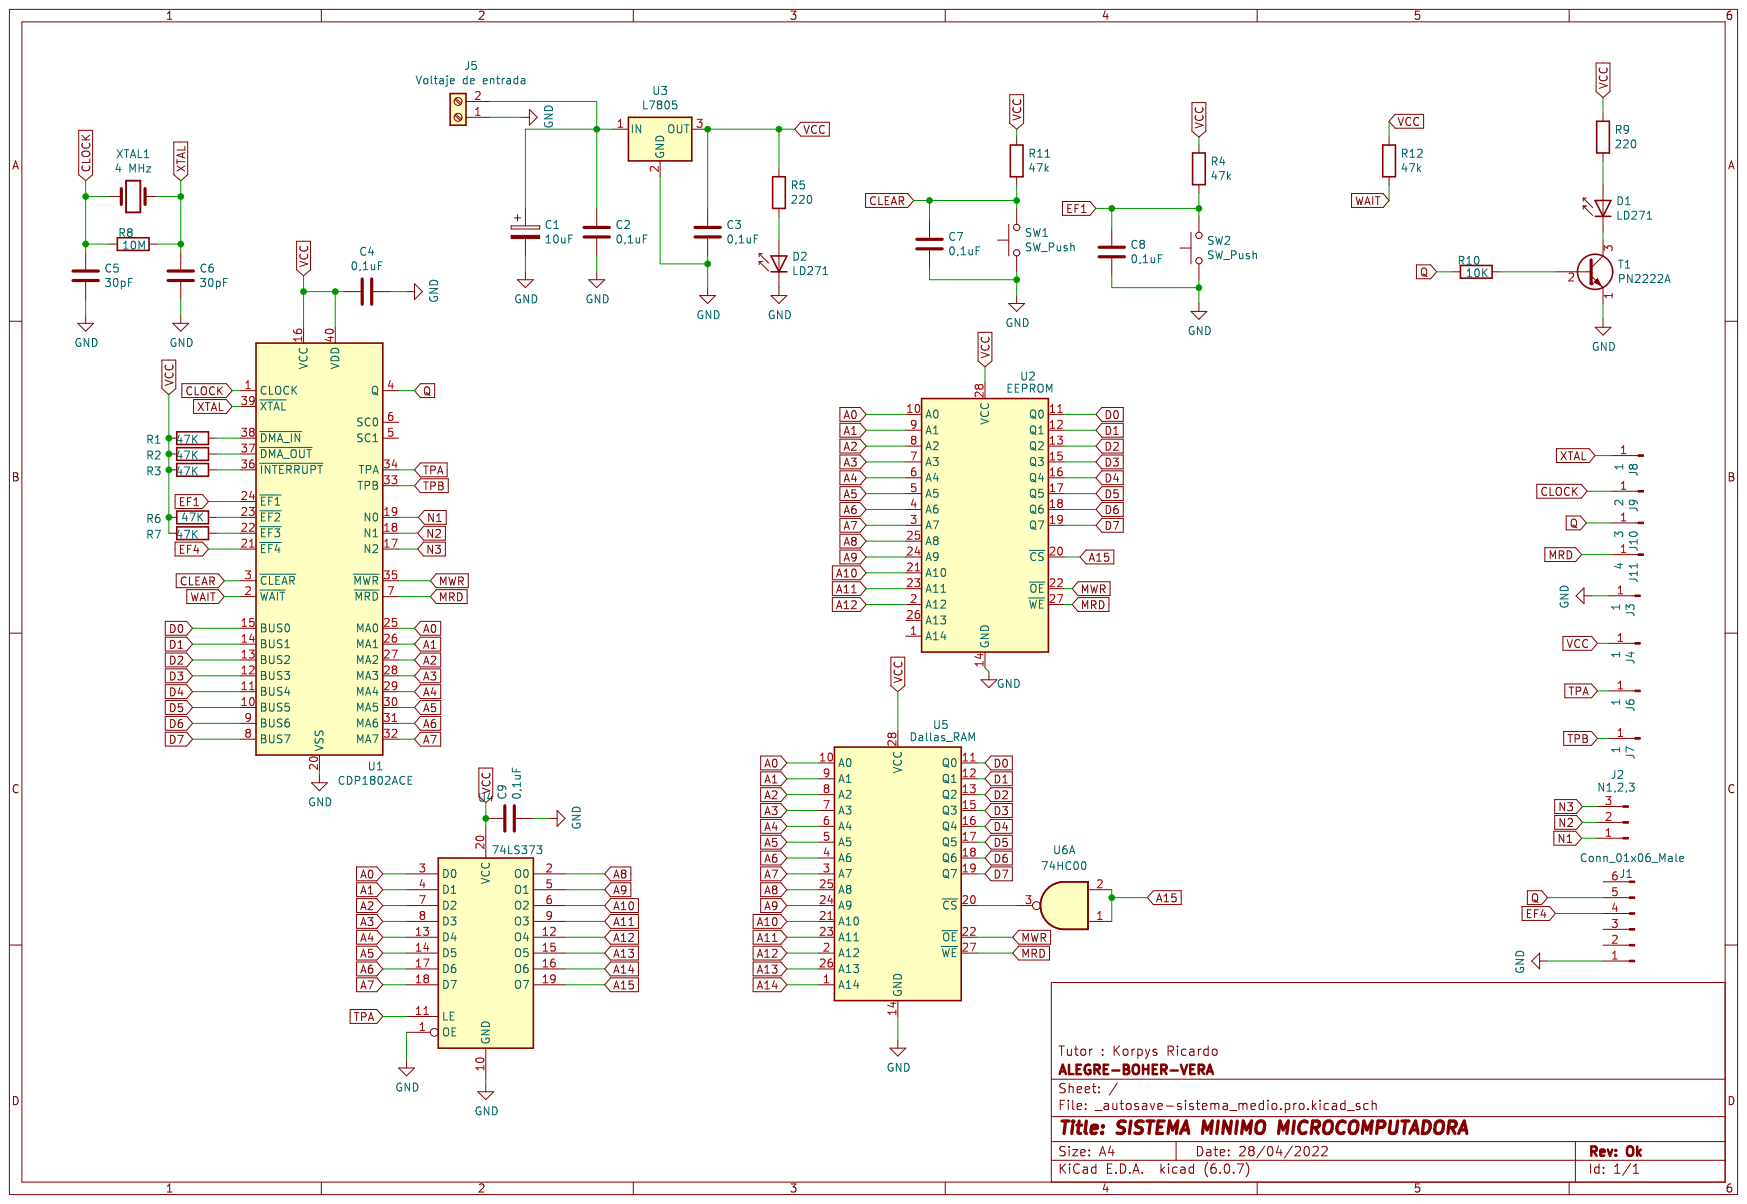
[picture p168: page 1]
