felipesantiagoach-ops/cdp1802-8bit-computer/archivos_de_kicad/3_Sistema_final/13-11_BOTTOM_SF.pdf

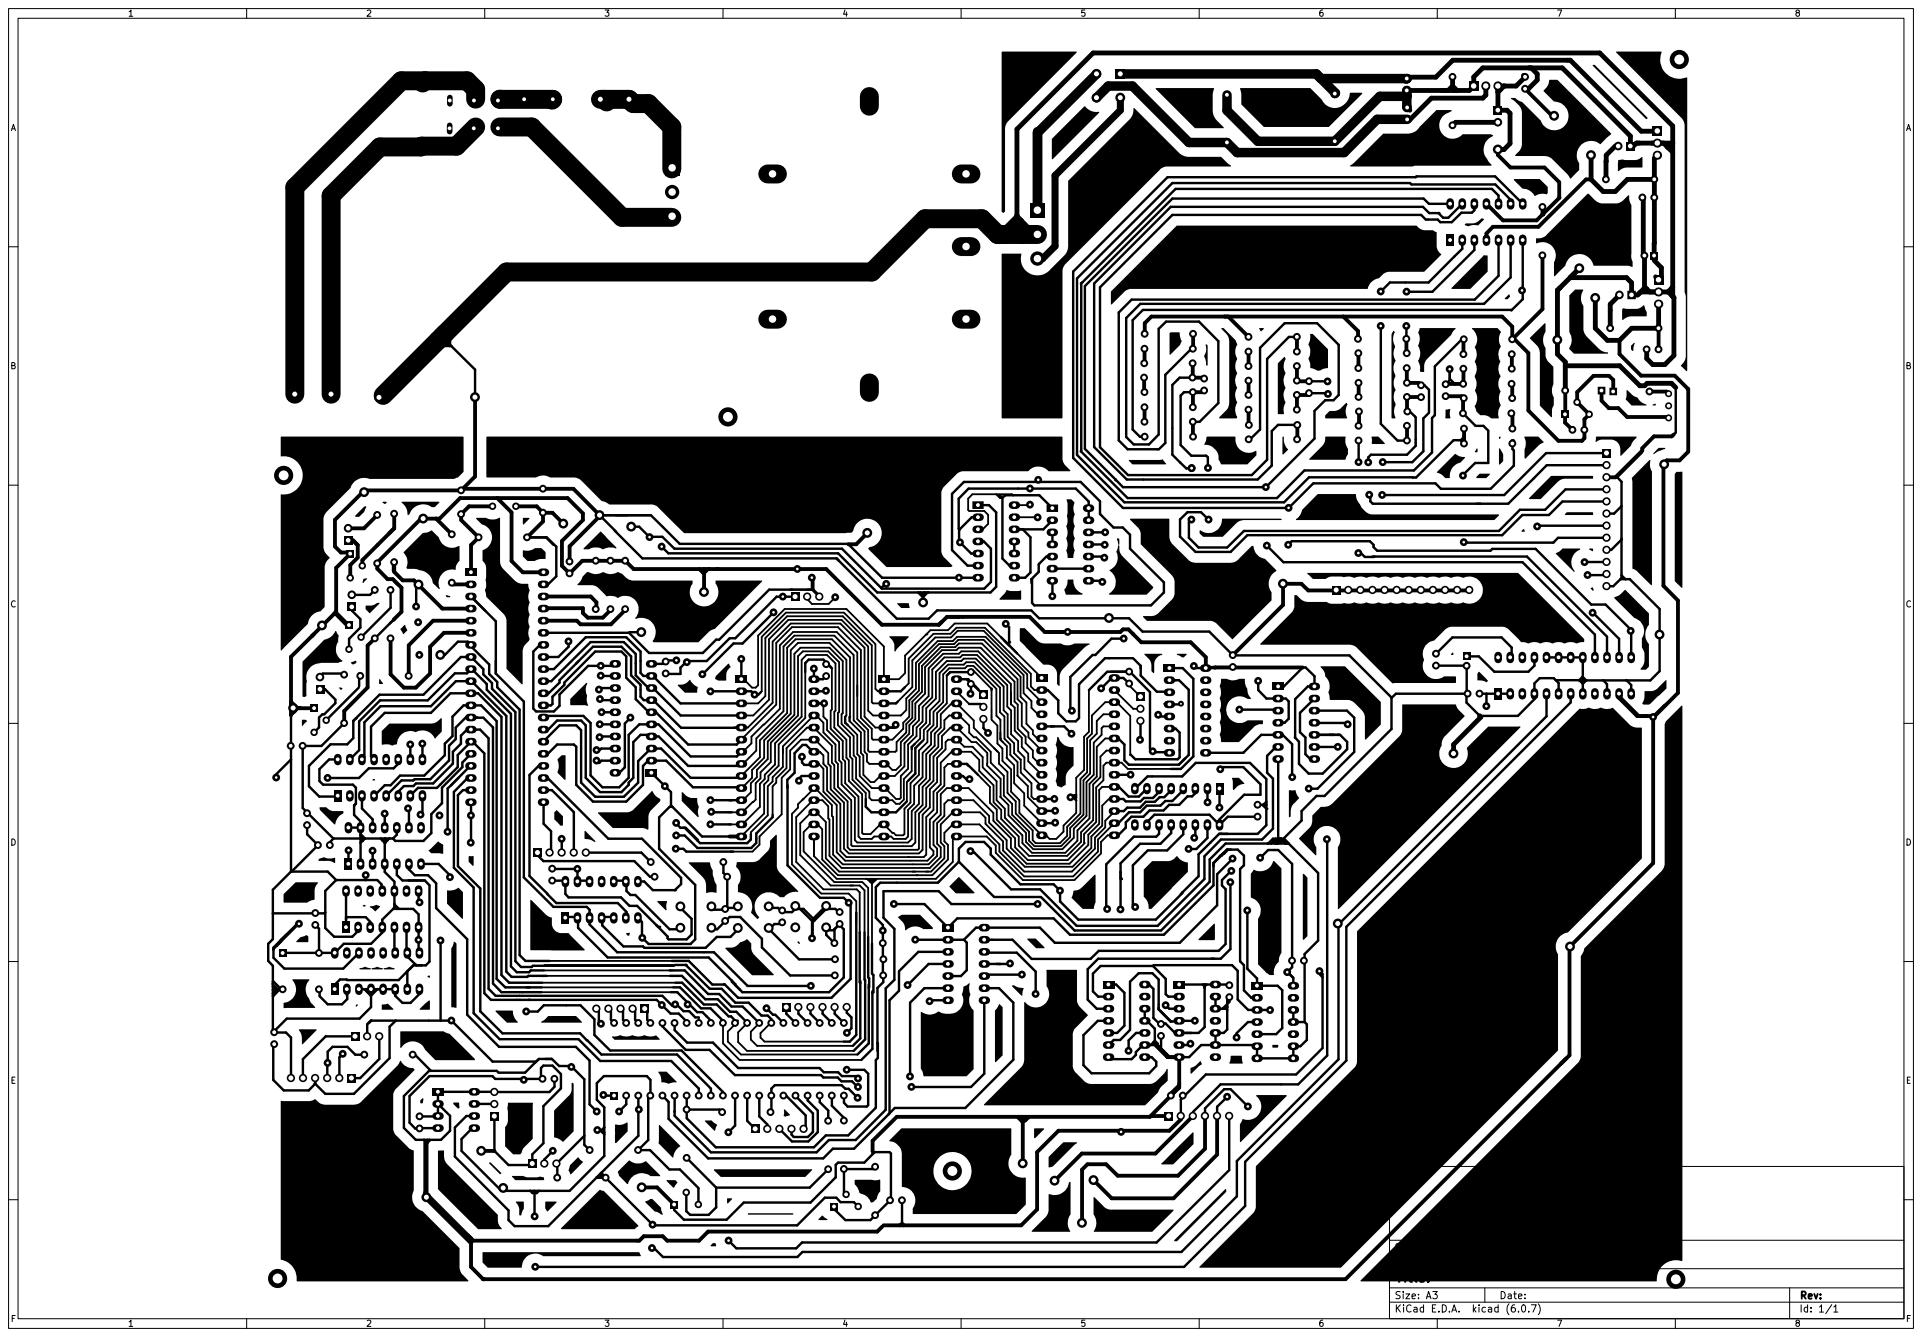
[picture p169: page 1]
