felipesantiagoach-ops/cdp1802-8bit-computer/archivos_de_kicad/3_Sistema_final/13-11_FRONT_SF.pdf

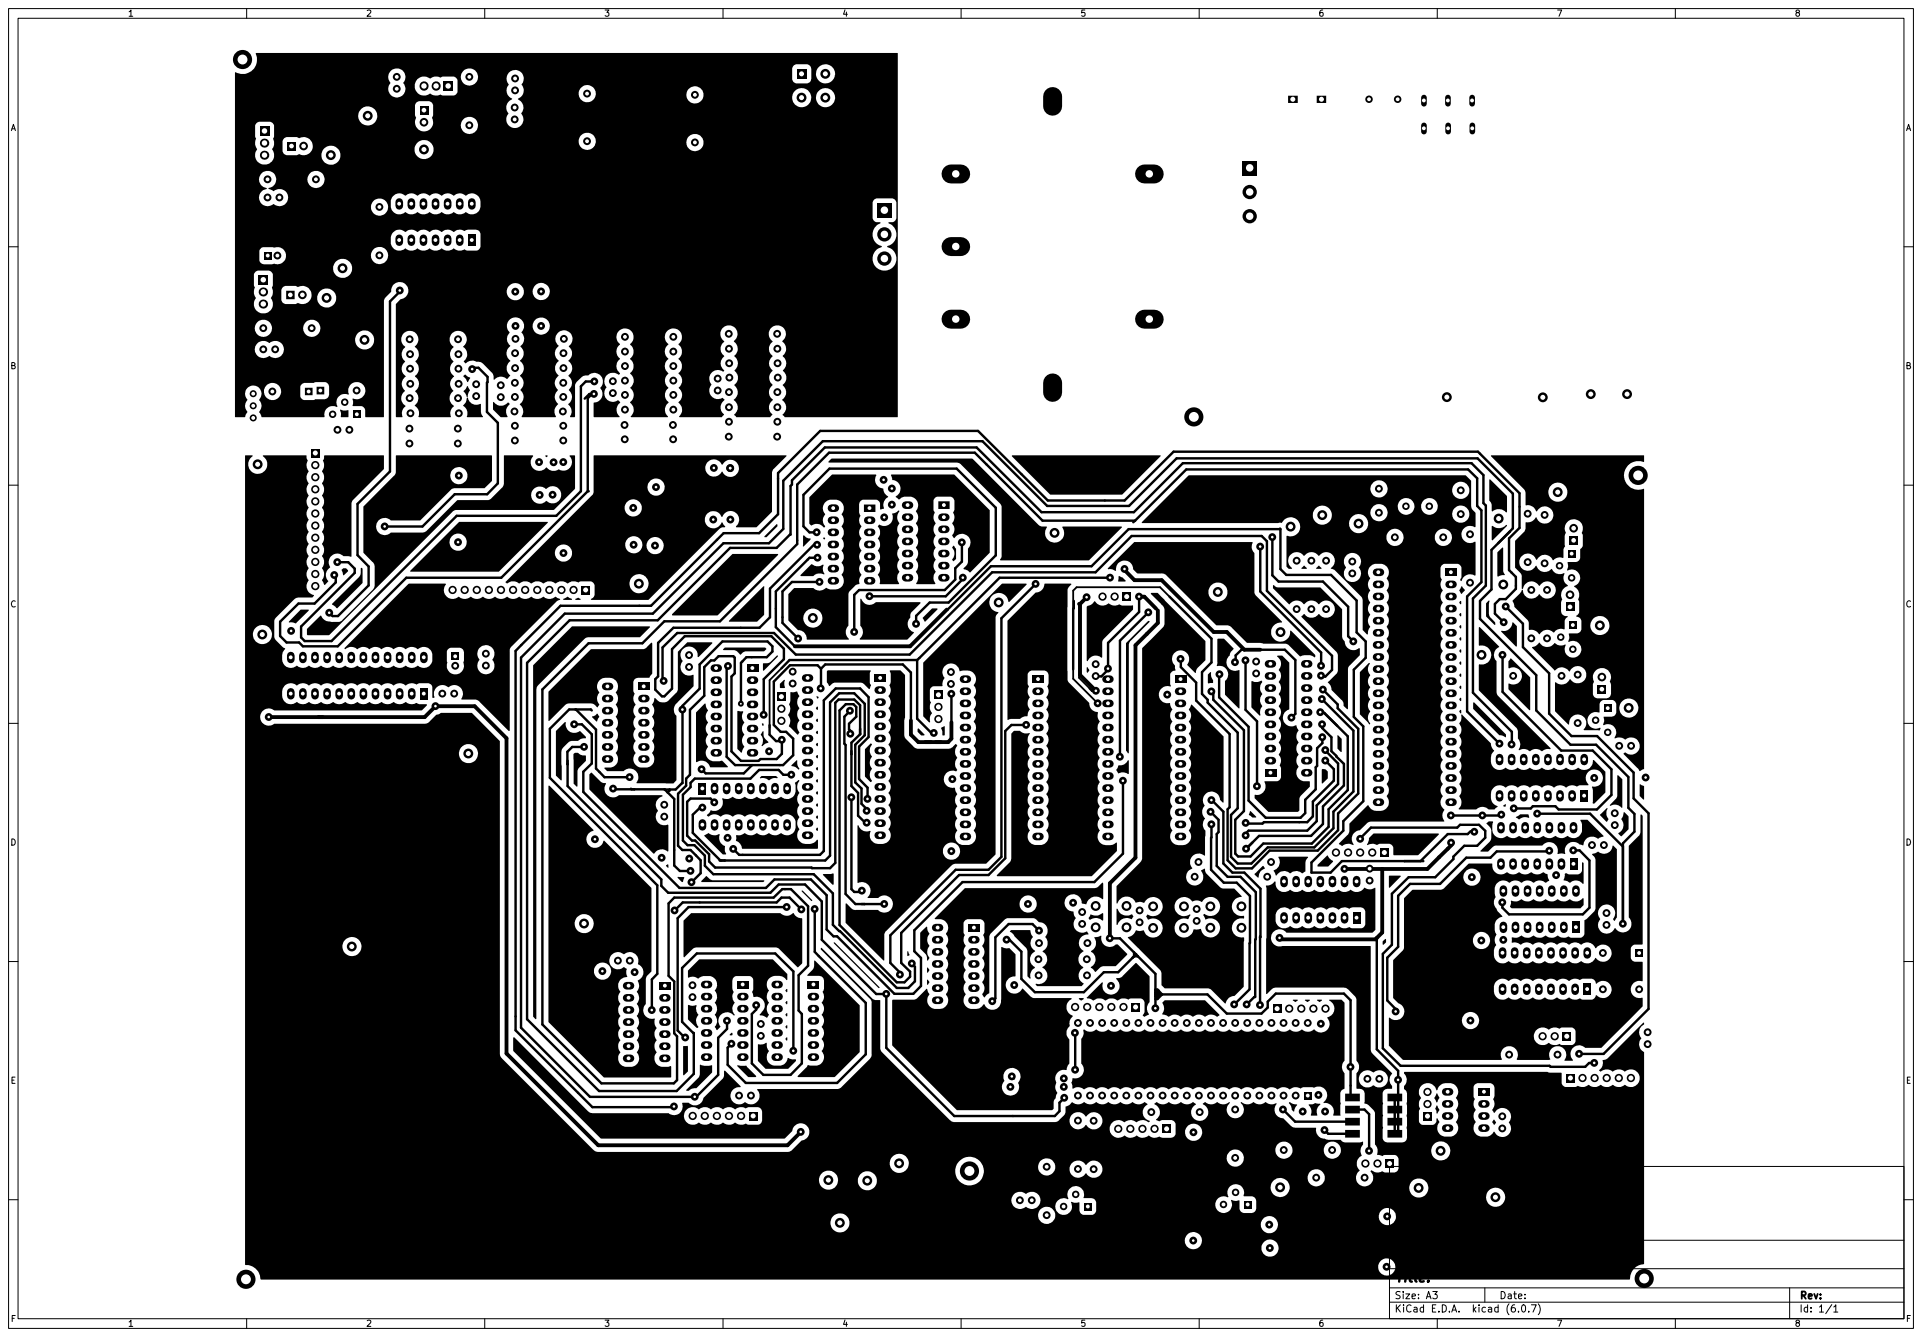
[picture p170: page 1]
