felipesantiagoach-ops/cdp1802-8bit-computer/archivos_de_kicad/3_Sistema_final/SISTEMA_FINAL_esquematico_segmentado/SISTEMA_FINAL_esquematico_segmentado.pdf

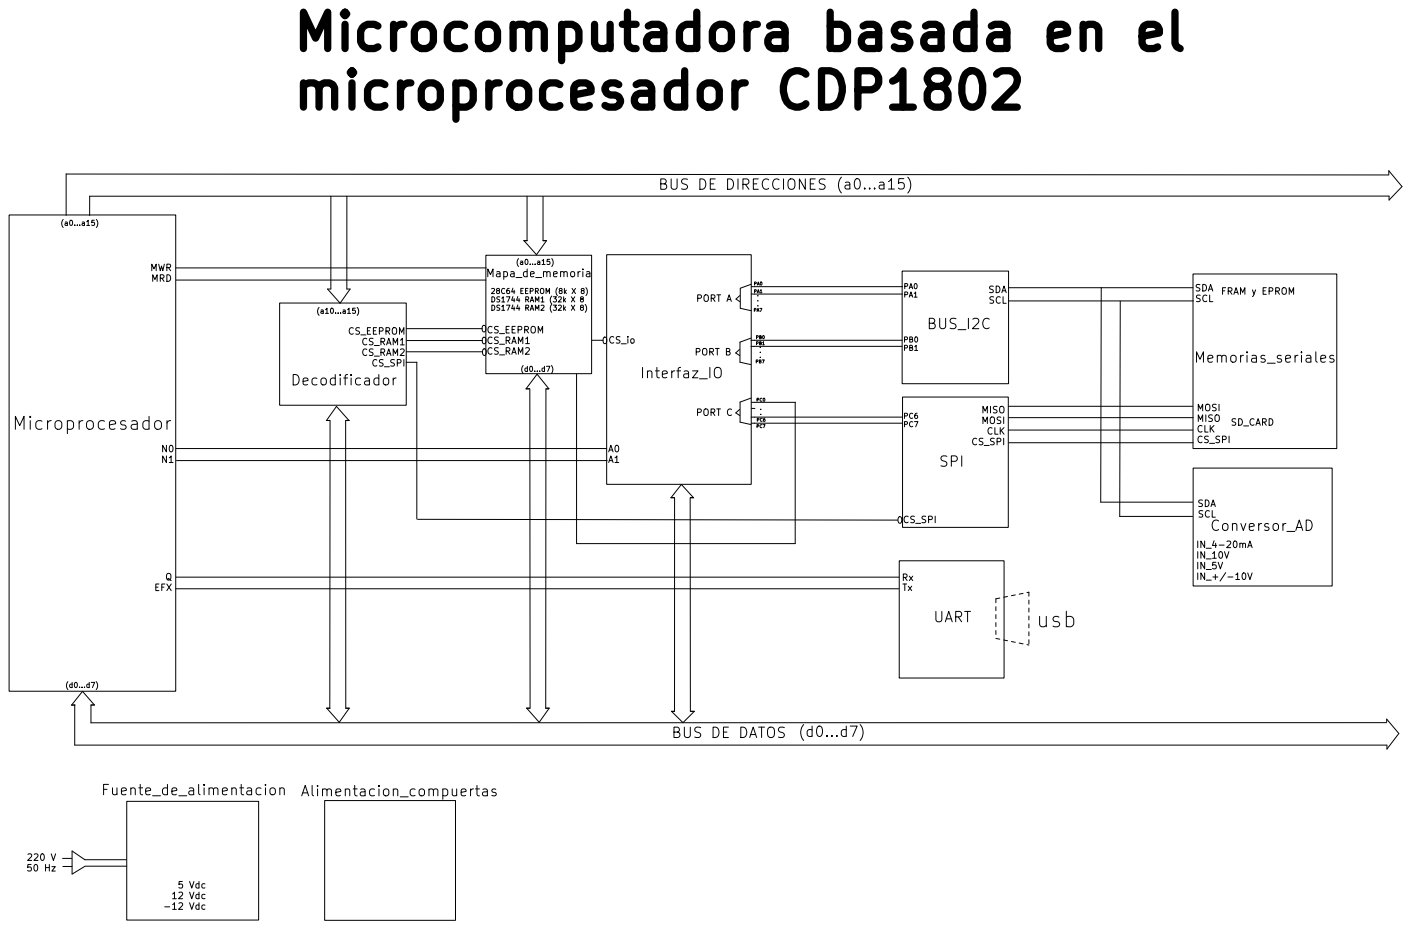
[picture p172: page 1]

PB7 PB0 Microcomputadora basada en el
microprocesador CDP1802
