felipesantiagoach-ops/cdp1802-8bit-computer/programas/FigForth/hart_figforth/1802reg.asm

;HRJ A18 wants register names defined...

R0		EQU	0
R1		EQU	1
R2		EQU	2
R3		EQU	3
R4		EQU	4
R5		EQU	5
R6		EQU	6
R7		EQU	7
R8		EQU	8
R9		EQU	9
R10		EQU	10
R11		EQU	11
R12		EQU	12
R13		EQU	13
R14		EQU	14
R15		EQU	15

r0		EQU	0
r1		EQU	1
r2		EQU	2
r3		EQU	3
r4		EQU	4
r5		EQU	5
r6		EQU	6
r7		EQU	7
r8		EQU	8
r9		EQU	9
ra		EQU	10
rb		EQU	11
rc		EQU	12
rd		EQU	13
re		EQU	14
rf		EQU	15

RA		EQU	10
RB		EQU	11
RC		EQU	12
RD		EQU	13
RE		EQU	14
RF		EQU	15
